disk91/WioLoRaWANFieldTester/helium_logo.h

/*  GIMP header image file format (RGB): /Users/paul/Desktop/helium-hnt-logo.h  */

static unsigned int helium_width = 100;
static unsigned int helium_height = 100;

/*  Call this macro repeatedly.  After each use, the pixel data can be extracted  */

#define HELIUM_PIXEL(data,pixel) {\
pixel[0] = (((data[0] - 33) << 2) | ((data[1] - 33) >> 4)); \
pixel[1] = ((((data[1] - 33) & 0xF) << 4) | ((data[2] - 33) >> 2)); \
pixel[2] = ((((data[2] - 33) & 0x3) << 6) | ((data[3] - 33))); \
data += 4; \
}
static const char *helium_data =
  "````````````````````````````````````````````````````````````````"
  "````````````````````````````````````````````````````````````````"
  "````````````````````````````````^0D`X_L`SN\\`L]\\`G]4`B,L`>L4`2+8`"
  "/+,`/+,`/+,`/+,`2+8`>L4`B,L`G]4`L]``SN\\`XOL`^0D`````````````````"
  "````````````````````````````````````````````````````````````````"
  "````````````````````````````````````````````````````````````````"
  "````````````````````````````````````````````````````````````````"
  "````````````````````````````````````````````````````````````````"
  "````````````````````````````````\\`4`SN\\`H]<`;;``/+,`/+,`/+,`/+,`"
  "/+,`/+,`/+,`/+,`/+,`/+,`/+,`/+,`/+,`/+,`/+,`/+,`/+,`/+,`/+,`/+,`"
  ";;``H]<`S>X`\\`4`````````````````````````````````````````````````"
  "````````````````````````````````````````````````````````````````"
  "````````````````````````````````````````````````````````````````"
  "````````````````````````````````````````````````````````````````"
  "````````````````````````````````````ZO``O.0`<\\(`/+,`/+,`/+,`/+,`"
  "/+,`/+,`/+,`/+,`/+,`/+,`/+,`/+,`/+,`/+,`/+,`/+,`/+,`/+,`/+,`/+,`"
  "/+,`/+,`/+,`/+,`/+,`/+,`/+,`/+,`<\\(`O.0`ZO``````````````````````"
  "````````````````````````````````````````````````````````````````"
  "````````````````````````````````````````````````````````````````"
  "````````````````````````````````````````````````````````````````"
  "````````````````````````````````````````^PH`R.L`>L4`/+,`/+,`/+,`"
  "/+,`/+,`/+,`/+,`/+,`/+,`/+,`/+,`/+,`/+,`/+,`/+,`/+,`/+,`/+,`/+,`"
  "/+,`/+,`/+,`/+,`/+,`/+,`/+,`/+,`/+,`/+,`/+,`/+,`/+,`/+,`/+,`><4`"
  "R.L`^PH`````````````````````````````````````````````````````````"
  "````````````````````````````````````````````````````````````````"
  "````````````````````````````````````````````````````````````````"
  "````````````````````````````````````````````````\\@0`L-X`3;<`/+,`"
  "/+,`/+,`/+,`/+,`/+,`/+,`/+,`/+,`/+,`/+,`/+,`/+,`/+,`/+,`/+,`/+,`"
  "/+,`/+,`/+,`/+,`/+,`/+,`/+,`/+,`/+,`/+,`/+,`/+,`/+,`/+,`/+,`/+,`"
  "/+,`/+,`/+,`/+,`/+,`3;<`K]T`\\@0`````````````````````````````````"
  "````````````````````````````````````````````````````````````````"
  "````````````````````````````````````````````````````````````````"
  "````````````````````````````````````````````````````````\\@0`J=H`"
  "/+,`/+,`/+,`/+,`/+,`/+,`/+,`/+,`/+,`/+,`/+,`/+,`/+,`/+,`/+,`/+,`"
  "/+,`/+,`/+,`/+,`/+,`/+,`/+,`/+,`/+,`/+,`/+,`/+,`/+,`/+,`/+,`/+,`"
  "/+,`/+,`/+,`/+,`/+,`/+,`/+,`/+,`/+,`/+,`/+,`/+,`J=H`\\@0`````````"
  "````````````````````````````````````````````````````````````````"
  "````````````````````````````````````````````````````````````````"
  "````````````````````````````````````````````````````````````````"
  "^`L`L]\\`0;0`/+,`/+,`/+,`/+,`/+,`/+,`/+,`/+,`/+,`/+,`/+,`/+,`/+,`"
  "/+,`/+,`/+,`/+,`/+,`/+,`/+,`/+,`/+,`/+,`/+,`/+,`/+,`/+,`/+,`/+,`"
  "/+,`/+,`/+,`/+,`/+,`/+,`/+,`/+,`/+,`/+,`/+,`/+,`/+,`/+,`/+,`/+,`"
  "/+,`0;0`L]\\`^`L`````````````````````````````````````````````````"
  "````````````````````````````````````````````````````````````````"
  "````````````````````````````````````````````````````````````````"
  "````````````T>``6[H`/+,`/+,`/+,`/+,`/+,`/+,`/+,`/+,`/+,`/+,`/+,`"
  "/+,`/+,`/+,`/+,`/+,`/+,`/+,`/+,`/+,`/+,`/+,`/+,`/+,`/+,`/+,`/+,`"
  "/+,`/+,`/+,`/+,`/+,`/+,`/+,`/+,`/+,`/+,`/+,`/+,`/+,`/+,`/+,`/+,`"
  "/+,`/+,`/+,`/+,`/+,`/+,`/+,`6[H`T>``````````````````````````````"
  "````````````````````````````````````````````````````````````````"
  "````````````````````````````````````````````````````````````````"
  "````````````````````]08`D\\\\`/+,`/+,`/+,`/+,`/+,`/+,`/+,`/+,`/+,`"
  "/+,`/+,`/+,`/+,`/+,`/+,`/+,`/+,`/+,`/+,`/+,`/+,`/+,`/+,`/+,`/+,`"
  "/+,`/+,`/+,`/+,`/+,`/+,`/+,`/+,`/+,`/+,`/+,`/+,`/+,`/+,`/+,`/+,`"
  "/+,`/+,`/+,`/+,`/+,`/+,`/+,`/+,`/+,`/+,`/+,`/+,`/+,`D\\\\`]08`````"
  "````````````````````````````````````````````````````````````````"
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
  "````````````Z?\\`<,$`/+,`/+,`/+,`/+,`/+,`/+,`/+,`5+@`V/4`````````"
  "````````G-0`/+,`/+,`/+,`/+,`/+,`/+,`/+,`/+,`/+,`/+,`/+,`/+,`/+,`"
  "/+,`L]\\`````````````````````````````````````````````\\@0`0;0`/+,`"
  "/+,`/+,`/+,`/+,`/+,`/+,`/+,`/+,`/+,`/+,`/+,`/+,`/+,`/+,`/+,`/+,`"
  "/+,`/+,`/+,`/+,`/+,`/+,`/+,`/+,`/+,`/+,`/+,`/+,`/+,`/+,`/+,`/+,`"
  "/+,`/+,`/+,`/+,`/+,`/+,`/+,`/+,`/+,`/+,`/+,`/+,`/+,`/+,`/+,`/+,`"
  "/+,`/+,`T.``````````````\\00`4[@`/+,`/+,`/+,`/+,`/+,`/+,`/+,`/+,`"
  "/+,`/+,`W/<`````````````[P,`/+,`/+,`/+,`/+,`/+,`/+,`/+,`/+,`/+,`"
  "/+,`/+,`/+,`/+,`/+,`0;0`\\@0`````````````````````````````````````"
  "````J=H`/+,`/+,`/+,`/+,`/+,`/+,`/+,`/+,`/+,`/+,`/+,`/+,`/+,`/+,`"
  "/+,`/+,`/+,`/+,`/+,`/+,`/+,`/+,`/+,`/+,`/+,`/+,`/+,`/+,`/+,`/+,`"
  "/+,`/+,`/+,`/+,`/+,`/+,`/+,`/+,`/+,`/+,`1K4`A,D`A\\H`DL\\`C<T`B,L`"
  "<,$`/+,`/+,`/+,`/+,`6+D`_PT`````````````@<@`/+,`/+,`/+,`/+,`/+,`"
  "/+,`/+,`/+,`/+,`/+,`/+,`6+D`^PH`````````````E,``/+,`/+,`/+,`/+,`"
  "/+,`/+,`/+,`/+,`/+,`/+,`/+,`/+,`/+,`/+,`J=H`````````````````````"
  "````````````````\\@0`/+,`/+,`/+,`/+,`/+,`/+,`/+,`/+,`/+,`/+,`/+,`"
  "/+,`/+,`/+,`/+,`/+,`/+,`/+,`/+,`/+,`/+,`/+,`/+,`/+,`/+,`/+,`/+,`"
  "/+,`/+,`/+,`/+,`/+,`/+,`/+,`/+,`/+,`/+,`7[L`J=H`V/4`\\`8`````````"
  "`````````````````````0X`Y_X`QNH`DL\\`H]<`````````````W/<`/+,`/+,`"
  "/+,`/+,`/+,`/+,`/+,`/+,`/+,`/+,`/+,`/+,`/+,`P.<`````````````RNP`"
  "/+,`/+,`/+,`/+,`/+,`/+,`/+,`/+,`/+,`/+,`/+,`/+,`/+,`/+,`/+,`\\@0`"
  "````````````````````````````````K]T`/+,`/+,`/+,`/+,`/+,`/+,`/+,`"
  "/+,`/+,`/+,`/+,`/+,`/+,`/+,`/+,`/+,`/+,`/+,`/+,`/+,`/+,`/+,`/+,`"
  "/+,`/+,`/+,`/+,`/+,`/+,`/+,`/+,`/+,`/+,`/+,`/+,`D<X`W/<``@\\`````"
  "`````````````````````````````````````````````````````@\\`````````"
  "````I=@`/+,`/+,`/+,`/+,`/+,`/+,`/+,`/+,`/+,`/+,`/+,`/+,`/+,`?<8`"
  "````````````Z?\\`/+,`/+,`/+,`/+,`/+,`/+,`/+,`/+,`/+,`/+,`/+,`/+,`"
  "/+,`/+,`/+,`L-X`````````````````````````````^PH`3;<`/+,`/+,`/+,`"
  "/+,`/+,`/+,`/+,`/+,`/+,`/+,`/+,`/+,`/+,`/+,`/+,`/+,`/+,`/+,`/+,`"
  "/+,`/+,`/+,`/+,`/+,`/+,`/+,`/+,`/+,`/+,`/+,`/+,`/+,`/+,`ALH`Y_X`"
  "````````````````````````````````````````````````````````````````"
  "````````````````````A<D`/+,`/+,`/+,`/+,`/+,`/+,`/+,`/+,`/+,`/+,`"
  "/+,`/+,`/+,`/+,`````````````]P@`/+,`/+,`/+,`/+,`/+,`/+,`/+,`/+,`"
  "/+,`/+,`/+,`/+,`/+,`/+,`/+,`3;<`^PH`````````````````````````R.L`"
  "/+,`/+,`/+,`/+,`/+,`/+,`/+,`/+,`/+,`/+,`/+,`/+,`/+,`/+,`/+,`/+,`"
  "/+,`/+,`/+,`/+,`/+,`/+,`/+,`/+,`/+,`/+,`/+,`/+,`/+,`/+,`/+,`/+,`"
  "4;<`RNP`````````````````````````````````````````````````````````"
  "````````````````````````````````````=<,`/+,`/+,`/+,`/+,`/+,`/+,`"
  "/+,`/+,`/+,`/+,`/+,`/+,`/+,`/+,`````````````_`T`/+,`/+,`/+,`/+,`"
  "/+,`/+,`/+,`/+,`/+,`/+,`/+,`/+,`/+,`/+,`/+,`/+,`R.L`````````````"
  "````````````><4`/+,`/+,`/+,`/+,`/+,`/+,`/+,`/+,`/+,`/+,`/+,`/+,`"
  "/+,`/+,`/+,`/+,`/+,`/+,`/+,`/+,`/+,`/+,`/+,`/+,`/+,`/+,`/+,`/+,`"
  "/+,`/+,`/+,`<L(`[P,`````````````````````````````````````````````"
  "````````````````````````````````````````````````````B,L`/+,`/+,`"
  "/+,`/+,`/+,`/+,`/+,`/+,`/+,`/+,`/+,`/+,`/+,`3[<`````````````\\P4`"
  "/+,`/+,`/+,`/+,`/+,`/+,`/+,`/+,`/+,`/+,`/+,`/+,`/+,`/+,`/+,`/+,`"
  ">L4`````````````````````ZO``/+,`/+,`/+,`/+,`/+,`/+,`/+,`/+,`/+,`"
  "/+,`/+,`/+,`/+,`/+,`/+,`/+,`/+,`/+,`/+,`/+,`/+,`/+,`/+,`/+,`/+,`"
  "/+,`/+,`/+,`/+,`/+,`/+,`CLT`^@H`````````````````````````````````"
  "````````````````````````````````````````````````````````````````"
  "````A\\H`/+,`/+,`/+,`/+,`/+,`/+,`/+,`/+,`/+,`/+,`/+,`/+,`/+,`F],`"
  "````````````Y/P`/+,`/+,`/+,`/+,`/+,`/+,`/+,`/+,`/+,`/+,`/+,`/+,`"
  "/+,`/+,`/+,`/+,`/+,`ZO``````````````````O.0`/+,`/+,`/+,`/+,`/+,`"
  "/+,`/+,`/+,`/+,`/+,`/+,`/+,`/+,`/+,`/+,`/+,`/+,`/+,`/+,`/+,`/+,`"
  "/+,`/+,`/+,`/+,`/+,`/+,`/+,`/+,`/+,`CLT`_PT`````````````````````"
  "````````````````````````````````````````````````````````````````"
  "````````````````_PT`5KD`/+,`/+,`/+,`/+,`/+,`/+,`/+,`/+,`/+,`/+,`"
  "/+,`/+,`/+,`V?4`````````````P^@`/+,`/+,`/+,`/+,`/+,`/+,`/+,`/+,`"
  "/+,`/+,`/+,`/+,`/+,`/+,`/+,`/+,`/+,`O.0`````````````````<\\(`/+,`"
  "/+,`/+,`/+,`/+,`/+,`/+,`/+,`/+,`/+,`/+,`/+,`/+,`/+,`/+,`/+,`/+,`"
  "/+,`/+,`/+,`/+,`/+,`/+,`/+,`/+,`/+,`/+,`/+,`/+,`<L(`^@D`````````"
  "`````````````````````````````````````P\\`Z/\\`S^\\`M-``L]\\`LM\\`O^8`"
  "U_0`]@<`````````````````````````MN$`/+,`/+,`/+,`/+,`/+,`/+,`/+,`"
  "/+,`/+,`/+,`/+,`/+,`/+,`D\\\\`````````````````?L8`/+,`/+,`/+,`/+,`"
  "/+,`/+,`/+,`/+,`/+,`/+,`/+,`/+,`/+,`/+,`/+,`/+,`/+,`<\\(`````````"
  "````\\`4`/+,`/+,`/+,`/+,`/+,`/+,`/+,`/+,`/+,`/+,`/+,`/+,`/+,`/+,`"
  "/+,`/+,`/+,`/+,`/+,`/+,`/+,`/+,`/+,`/+,`/+,`/+,`/+,`/+,`/+,`4;<`"
  "[@(`````````````````````````````````````````\\00`L=\\`7;L`/+,`/+,`"
  "/+,`/+,`/+,`/+,`/+,`/+,`@L@`S^\\`_@P`````\\`4`J=H`/+,`/+,`/+,`/+,`"
  "/+,`/+,`/+,`/+,`/+,`/+,`/+,`/+,`/+,`<\\(`]`@`````````````X?H`/+,`"
  "/+,`/+,`/+,`/+,`/+,`/+,`/+,`/+,`/+,`/+,`/+,`/+,`/+,`/+,`/+,`/+,`"
  "/+,`/+,`\\`4`````````S>X`/+,`/+,`/+,`/+,`/+,`/+,`/+,`/+,`/+,`/+,`"
  "/+,`/+,`/+,`/+,`/+,`/+,`/+,`/+,`/+,`/+,`/+,`/+,`/+,`/+,`/+,`/+,`"
  "/+,`/+,`/+,`R.L`````````````````````````````````````^`L`KMT`/+,`"
  "/+,`/+,`/+,`/+,`/+,`/+,`/+,`/+,`/+,`/+,`/+,`/+,`/+,`/+,`/+,`/+,`"
  "/+,`/+,`/+,`/+,`/+,`/+,`/+,`/+,`/+,`/+,`/+,`/+,`I-@`_0L`````````"
  "`````0X`?\\<`/+,`/+,`/+,`/+,`/+,`/+,`/+,`/+,`/+,`/+,`/+,`/+,`/+,`"
  "/+,`/+,`/+,`/+,`/+,`/+,`SN\\`````````H]<`/+,`/+,`/+,`/+,`/+,`/+,`"
  "/+,`/+,`/+,`/+,`/+,`/+,`/+,`/+,`/+,`/+,`/+,`/+,`/+,`/+,`/+,`/+,`"
  "/+,`/+,`/+,`/+,`/+,`/+,`@L@``P\\`````````````````````````````````"
  "Z/X`;;``/+,`/+,`/+,`/+,`/+,`/+,`/+,`/+,`/+,`/+,`/+,`/+,`/+,`/+,`"
  "/+,`/+,`/+,`/+,`/+,`/+,`/+,`/+,`/+,`<L(`IMD`FM,`ALH`F-(`O^8`[@(`"
  "````````````````````L]``/+,`/+,`/+,`/+,`/+,`/+,`/+,`/+,`/+,`/+,`"
  "/+,`/+,`/+,`/+,`/+,`/+,`/+,`/+,`/+,`/+,`H]<`````````;;``/+,`/+,`"
  "/+,`/+,`/+,`/+,`/+,`/+,`/+,`/+,`/+,`/+,`/+,`/+,`/+,`/+,`/+,`/+,`"
  "/+,`/+,`/+,`/+,`/+,`/+,`/+,`/+,`/+,`/+,`XOL`````````````````````"
  "````````````X_P`4;<`/+,`/+,`/+,`/+,`/+,`/+,`/+,`/+,`/+,`/+,`/+,`"
  "/+,`/+,`/+,`/+,`/+,`/+,`/+,`/+,`/+,`/+,`/+,`4;<`U_0`````````````"
  "````````````````````````````````P.<`/+,`/+,`/+,`/+,`/+,`/+,`/+,`"
  "/+,`/+,`/+,`/+,`/+,`/+,`/+,`/+,`/+,`/+,`/+,`/+,`/+,`/+,`;;``````"
  "^0D`/+,`/+,`/+,`/+,`/+,`/+,`/+,`/+,`/+,`/+,`/+,`/+,`/+,`/+,`/+,`"
  "/+,`/+,`/+,`/+,`/+,`/+,`/+,`/+,`/+,`/+,`/+,`/+,`/+,`BLP`````````"
  "````````````````````````Z/X`4[@`/+,`/+,`/+,`/+,`/+,`/+,`/+,`/+,`"
  "/+,`/+,`/+,`/+,`/+,`/+,`/+,`/+,`/+,`/+,`/+,`/+,`/+,`/+,`/+,`SN\\`"
  "````````````````````````````````````````_@P`IM@`/+,`/+,`/+,`/+,`"
  "/+,`/+,`/+,`/+,`/+,`/+,`/+,`/+,`/+,`/+,`/+,`/+,`/+,`/+,`/+,`/+,`"
  "/+,`/+,`/+,`^0D`X_L`/+,`/+,`/+,`/+,`/+,`/+,`/+,`/+,`/+,`/+,`/+,`"
  "/+,`/+,`/+,`/+,`/+,`/+,`/+,`/+,`/+,`/+,`/+,`/+,`/+,`/+,`/+,`/+,`"
  "/+,`UO0`````````````````````````````^`L`;;``/+,`/+,`/+,`/+,`/+,`"
  "/+,`/+,`/+,`/+,`<,$`B,L`B,L`>,0`/+,`/+,`/+,`/+,`/+,`/+,`/+,`/+,`"
  "/+,`/+,`6KH``@\\`````````````````````````````````_PT`T.``8[T`/+,`"
  "/+,`/+,`/+,`/+,`/+,`/+,`/+,`/+,`/+,`/+,`/+,`/+,`/+,`/+,`/+,`/+,`"
  "/+,`/+,`/+,`/+,`/+,`/+,`/+,`X_L`SN\\`/+,`/+,`/+,`/+,`/+,`/+,`/+,`"
  "/+,`/+,`/+,`/+,`/+,`/+,`/+,`/+,`/+,`/+,`/+,`/+,`/+,`/+,`/+,`/+,`"
  "/+,`/+,`/+,`/+,`5KD`_`T`````````````````````````````K]T`/+,`/+,`"
  "/+,`/+,`/+,`/+,`/+,`4[@`NN,`\\`8`````````````````^0D`QNH`7;L`/+,`"
  "/+,`/+,`/+,`/+,`/+,`/+,`BLP``````````````````````````````P\\`J=H`"
  "6[H`/+,`/+,`/+,`/+,`/+,`/+,`/+,`/+,`/+,`/+,`/+,`/+,`/+,`/+,`/+,`"
  "/+,`/+,`/+,`/+,`/+,`/+,`/+,`/+,`/+,`/+,`/+,`SN\\`L]``/+,`/+,`/+,`"
  "/+,`/+,`/+,`/+,`/+,`/+,`/+,`/+,`/+,`/+,`/+,`/+,`/+,`/+,`/+,`/+,`"
  "/+,`/+,`/+,`/+,`/+,`/+,`/+,`/+,`HM<`````````````````````````````"
  "\\@0`/+,`/+,`/+,`/+,`/+,`/+,`/+,`A<D`]08`````````````````````````"
  "````````^@D`D\\\\`/+,`/+,`/+,`/+,`/+,`/+,`6KH``P\\`````````````````"
  "````````````B\\P`/+,`/+,`/+,`/+,`/+,`/+,`/+,`/+,`/+,`/+,`/+,`/+,`"
  "/+,`/+,`/+,`/+,`/+,`/+,`/+,`/+,`/+,`/+,`/+,`/+,`/+,`/+,`/+,`L]``"
  "G]4`/+,`/+,`/+,`/+,`/+,`/+,`/+,`/+,`/+,`/+,`/+,`/+,`/+,`/+,`/+,`"
  "/+,`/+,`/+,`/+,`/+,`/+,`/+,`/+,`/+,`/+,`/+,`/+,`T.``````````````"
  "````````````````MN$`/+,`/+,`/+,`/+,`/+,`/+,`A,D`_PT`````````````"
  "````````````````````````````_`T`D\\\\`/+,`/+,`/+,`/+,`/+,`/+,`V_8`"
  "````````````````````````````P^@`/+,`/+,`/+,`/+,`/+,`/+,`/+,`/+,`"
  "/+,`/+,`/+,`/+,`/+,`/+,`/+,`/+,`/+,`/+,`/+,`/+,`/+,`/+,`/+,`/+,`"
  "/+,`/+,`/+,`G]4`B,L`/+,`/+,`/+,`/+,`/+,`/+,`/+,`/+,`/+,`/+,`/+,`"
  "/+,`/+,`/+,`/+,`/+,`/+,`/+,`/+,`/+,`/+,`/+,`/+,`/+,`/+,`/+,`/+,`"
  "[@$`````````````````````````````8[T`/+,`/+,`/+,`/+,`/+,`4;<`\\`8`"
  "````````````````````````````````````````````````^@D`7;L`/+,`/+,`"
  "/+,`/+,`/+,`GM4`````````````````````````````Y/P`/+,`/+,`/+,`/+,`"
  "/+,`/+,`/+,`/+,`/+,`/+,`/+,`/+,`/+,`/+,`/+,`/+,`/+,`/+,`/+,`/+,`"
  "/+,`/+,`/+,`/+,`/+,`/+,`/+,`B,L`>L4`/+,`/+,`/+,`/+,`/+,`/+,`/+,`"
  "/+,`/+,`/+,`/+,`/+,`/+,`/+,`/+,`/+,`/+,`/+,`/+,`/+,`/+,`/+,`/+,`"
  "/+,`/+,`/+,`/+,``P\\`````````````````````````[@$`/+,`/+,`/+,`/+,`"
  "/+,`/+,`N.(`````````````````````````````````````````````````````"
  "````R>L`/+,`/+,`/+,`/+,`/+,`1K4``0X`````````````````````````_@P`"
  "/+,`/+,`/+,`/+,`/+,`/+,`/+,`/+,`/+,`/+,`/+,`/+,`/+,`/+,`/+,`/+,`"
  "/+,`/+,`/+,`/+,`/+,`/+,`/+,`/+,`/+,`/+,`/+,`>L4`2+8`/+,`/+,`/+,`"
  "/+,`/+,`/+,`/+,`/+,`/+,`/+,`/+,`/+,`/+,`/+,`/+,`/+,`/+,`/+,`/+,`"
  "/+,`/+,`/+,`/+,`/+,`/+,`/+,`:+X`````````````````````````````T_(`"
  "/+,`/+,`/+,`/+,`/+,`/+,`\\00`````````````````````````````````````"
  "````````````````````^@H`/+,`/+,`/+,`/+,`/+,`/+,`Z?\\`````````````"
  "````````````````7;L`/+,`/+,`/+,`/+,`/+,`/+,`/+,`/+,`/+,`/+,`/+,`"
  "/+,`/+,`/+,`/+,`/+,`/+,`/+,`/+,`/+,`/+,`/+,`/+,`/+,`/+,`/+,`2+8`"
  "/+,`/+,`/+,`/+,`/+,`/+,`/+,`/+,`/+,`/+,`/+,`/+,`/+,`/+,`/+,`/+,`"
  "/+,`/+,`/+,`/+,`/+,`/+,`/+,`/+,`/+,`/+,`/+,`BLP`````````````````"
  "````````````O^8`/+,`/+,`/+,`/+,`/+,`8+P`````````````````````````"
  "````````````````````````````````````````@<@`/+,`/+,`/+,`/+,`/+,`"
  "TO$`````````````````````````````B<L`/+,`/+,`/+,`/+,`/+,`/+,`/+,`"
  "/+,`/+,`/+,`/+,`/+,`/+,`/+,`/+,`/+,`/+,`/+,`/+,`/+,`/+,`/+,`/+,`"
  "/+,`/+,`/+,`/+,`/+,`/+,`/+,`/+,`/+,`/+,`/+,`/+,`/+,`/+,`/+,`/+,`"
  "/+,`/+,`/+,`/+,`/+,`/+,`/+,`/+,`/+,`/+,`/+,`/+,`/+,`/+,`/+,`B,L`"
  "````````````````````````````L-X`/+,`/+,`/+,`/+,`/+,`B,L`````````"
  "````````````````````````````````````````````````````````G-0`/+,`"
  "/+,`/+,`/+,`/+,`TO$`````````````````````````````ALH`/+,`/+,`/+,`"
  "/+,`/+,`/+,`/+,`/+,`/+,`/+,`/+,`/+,`/+,`/+,`/+,`/+,`/+,`/+,`/+,`"
  "/+,`/+,`/+,`/+,`/+,`/+,`/+,`/+,`/+,`/+,`/+,`/+,`/+,`/+,`/+,`/+,`"
  "/+,`/+,`/+,`/+,`/+,`/+,`/+,`/+,`/+,`/+,`/+,`/+,`/+,`/+,`/+,`/+,`"
  "/+,`/+,`/+,`B<L`````````````````````````````M=``/+,`/+,`/+,`/+,`"
  "/+,`B<L`````````````````````````````````````````````````````````"
  "````````G=0`/+,`/+,`/+,`/+,`/+,`TO$`````````````````````````````"
  "ALH`/+,`/+,`/+,`/+,`/+,`/+,`/+,`/+,`/+,`/+,`/+,`/+,`/+,`/+,`/+,`"
  "/+,`/+,`/+,`/+,`/+,`/+,`/+,`/+,`/+,`/+,`/+,`/+,`/+,`/+,`/+,`/+,`"
  "/+,`/+,`/+,`/+,`/+,`/+,`/+,`/+,`/+,`/+,`/+,`/+,`/+,`/+,`/+,`/+,`"
  "/+,`/+,`/+,`/+,`/+,`/+,`/+,`?\\<`````````````````````````````SN\\`"
  "/+,`/+,`/+,`/+,`/+,`7[L`````````````````````````````````````````"
  "````````````````````````@L@`/+,`/+,`/+,`/+,`/+,`TO$`````````````"
  "````````````````B,L`/+,`/+,`/+,`/+,`/+,`/+,`/+,`/+,`/+,`/+,`/+,`"
  "/+,`/+,`/+,`/+,`/+,`/+,`/+,`/+,`/+,`/+,`/+,`/+,`/+,`/+,`/+,`/+,`"
  "2+8`/+,`/+,`/+,`/+,`/+,`/+,`/+,`/+,`/+,`/+,`/+,`/+,`/+,`/+,`/+,`"
  "/+,`/+,`/+,`/+,`/+,`/+,`/+,`/+,`/+,`/+,`/+,`0;0`````````````````"
  "````````````X?H`/+,`/+,`/+,`/+,`/+,`/+,`[`,`````````````````````"
  "````````````````````````````````````^`L`/+,`/+,`/+,`/+,`/+,`/+,`"
  "Y_X`````````````````````````````=<,`/+,`/+,`/+,`/+,`/+,`/+,`/+,`"
  "/+,`/+,`/+,`/+,`/+,`/+,`/+,`/+,`/+,`/+,`/+,`/+,`/+,`/+,`/+,`/+,`"
  "/+,`/+,`/+,`2+8`>L4`/+,`/+,`/+,`/+,`/+,`/+,`/+,`/+,`/+,`/+,`/+,`"
  "/+,`/+,`/+,`/+,`/+,`/+,`/+,`/+,`/+,`/+,`/+,`/+,`/+,`/+,`/+,`/+,`"
  "]@<`````````````````````````_0L`/+,`/+,`/+,`/+,`/+,`/+,`MN$`````"
  "````````````````````````````````````````````````````R^T`/+,`/+,`"
  "/+,`/+,`/+,`/[0`_@P``````````````````````````P\\`/+,`/+,`/+,`/+,`"
  "/+,`/+,`/+,`/+,`/+,`/+,`/+,`/+,`/+,`/+,`/+,`/+,`/+,`/+,`/+,`/+,`"
  "/+,`/+,`/+,`/+,`/+,`/+,`/+,`>L4`B,L`/+,`/+,`/+,`/+,`/+,`/+,`/+,`"
  "/+,`/+,`/+,`/+,`/+,`/+,`/+,`/+,`/+,`/+,`/+,`/+,`/+,`/+,`/+,`/+,`"
  "/+,`/+,`/+,`/+,`W?@`````````````````````````````EM$`/+,`/+,`/+,`"
  "/+,`/+,`3[<`\\P4`````````````````````````````````````````````````"
  "^PH`8+P`/+,`/+,`/+,`/+,`/+,`E,``````````````````````````````[@(`"
  "/+,`/+,`/+,`/+,`/+,`/+,`/+,`/+,`/+,`/+,`/+,`/+,`/+,`/+,`/+,`/+,`"
  "/+,`/+,`/+,`/+,`/+,`/+,`/+,`/+,`/+,`/+,`/+,`B,L`G]4`/+,`/+,`/+,`"
  "/+,`/+,`/+,`/+,`/+,`/+,`/+,`/+,`/+,`/+,`/+,`/+,`/+,`/+,`/+,`/+,`"
  "/+,`/+,`/+,`/+,`/+,`/+,`/+,`/+,`N>,`````````````````````````````"
  "V/4`/+,`/+,`/+,`/+,`/+,`/+,`@L@`_PT`````````````````````````````"
  "````````````_`T`D\\\\`/+,`/+,`/+,`/+,`/+,`/+,`T_(`````````````````"
  "````````````S^\\`/+,`/+,`/+,`/+,`/+,`/+,`/+,`/+,`/+,`/+,`/+,`/+,`"
  "/+,`/+,`/+,`/+,`/+,`/+,`/+,`/+,`/+,`/+,`/+,`/+,`/+,`/+,`/+,`G]4`"
  "L]``/+,`/+,`/+,`/+,`/+,`/+,`/+,`/+,`/+,`/+,`/+,`/+,`/+,`/+,`/+,`"
  "/+,`/+,`/+,`/+,`/+,`/+,`/+,`/+,`/+,`/+,`/+,`/+,`<L(`````````````"
  "`````````````````@\\`0;0`/+,`/+,`/+,`/+,`/+,`/+,`A<D`]08`````````"
  "````````````````````````^@D`D\\\\`/+,`/+,`/+,`/+,`/+,`/+,`:+X`_`T`"
  "````````````````````````````H-8`/+,`/+,`/+,`/+,`/+,`/+,`/+,`/+,`"
  "/+,`/+,`/+,`/+,`/+,`/+,`/+,`/+,`/+,`/+,`/+,`/+,`/+,`/+,`/+,`/+,`"
  "/+,`/+,`/+,`L]``SN\\`/+,`/+,`/+,`/+,`/+,`/+,`/+,`/+,`/+,`/+,`/+,`"
  "/+,`/+,`/+,`/+,`/+,`/+,`/+,`/+,`/+,`/+,`/+,`/+,`/+,`/+,`/+,`5KD`"
  "HM<`^@H`````````````````````````````7;L`/+,`/+,`/+,`/+,`/+,`/+,`"
  "/+,`4[@`NN,`\\`8`````````````````^0D`QNH`7;L`/+,`/+,`/+,`/+,`/+,`"
  "/+,`/+,`U/(`````````````````````````````_@P`4;<`/+,`/+,`/+,`/+,`"
  "/+,`/+,`/+,`/+,`/+,`/+,`/+,`/+,`/+,`/+,`/+,`/+,`/+,`/+,`/+,`/+,`"
  "/+,`/+,`/+,`/+,`/+,`/+,`/+,`SN\\`X_L`/+,`/+,`/+,`/+,`/+,`/+,`/+,`"
  "/+,`/+,`/+,`/+,`/+,`/+,`/+,`/+,`/+,`/+,`/+,`/+,`/+,`/+,`/+,`/+,`"
  "/+,`9;T`S^\\`_PT`````````````````````````````````^@D`/+,`/+,`/+,`"
  "/+,`/+,`/+,`/+,`/+,`/+,`/+,`/+,`<,$`B,L`B,L`>,0`/+,`/+,`/+,`/+,`"
  "/+,`/+,`/+,`/+,`/+,`F],`````````````````````````````````T_(`/+,`"
  "/+,`/+,`/+,`/+,`/+,`/+,`/+,`/+,`/+,`/+,`/+,`/+,`/+,`/+,`/+,`/+,`"
  "/+,`/+,`/+,`/+,`/+,`/+,`/+,`/+,`/+,`/+,`/+,`X_L`^0D`/+,`/+,`/+,`"
  "/+,`/+,`/+,`/+,`/+,`/+,`/+,`/+,`/+,`/+,`/+,`/+,`/+,`/+,`/+,`/+,`"
  "/+,`/+,`/+,`/+,`I-@`_@P`````````````````````````````````````````"
  "M=``/+,`/+,`/+,`/+,`/+,`/+,`/+,`/+,`/+,`/+,`/+,`/+,`/+,`/+,`/+,`"
  "/+,`/+,`/+,`/+,`/+,`/+,`/+,`/+,`=L,`_0L`````````````````````````"
  "````````@\\D`/+,`/+,`/+,`/+,`/+,`/+,`/+,`/+,`/+,`/+,`/+,`/+,`/+,`"
  "/+,`/+,`/+,`/+,`/+,`/+,`/+,`/+,`/+,`/+,`/+,`/+,`/+,`/+,`/+,`^0D`"
  "````;;``/+,`/+,`/+,`/+,`/+,`/+,`/+,`/+,`/+,`/+,`/+,`/+,`/+,`/+,`"
  "/+,`/+,`/+,`/+,`/+,`/+,`/+,`L]``````````````````````````````````"
  "````````_@P`NN,`/+,`/+,`/+,`/+,`/+,`/+,`/+,`/+,`/+,`/+,`/+,`/+,`"
  "/+,`/+,`/+,`/+,`/+,`/+,`/+,`/+,`/+,`/+,`/+,`>,0`]@<`````````````"
  "````````````````````V_8`/+,`/+,`/+,`/+,`/+,`/+,`/+,`/+,`/+,`/+,`"
  "/+,`/+,`/+,`/+,`/+,`/+,`/+,`/+,`/+,`/+,`/+,`/+,`/+,`/+,`/+,`/+,`"
  "/+,`/+,`;;``````````H]<`/+,`/+,`/+,`/+,`/+,`/+,`/+,`/+,`/+,`/+,`"
  "/+,`/+,`/+,`/+,`/+,`/+,`/+,`/+,`/+,`/+,`K-P`````````````````_`T`"
  "T.``E]$`5KD`/+,`;+``B<L`2+8`/+,`/+,`/+,`/+,`/+,`/+,`/+,`/+,`/+,`"
  "/+,`/+,`/+,`/+,`/+,`/+,`/+,`/+,`/+,`/+,`/+,`/+,`/+,`/+,`G]4`_@P`"
  "`````````````````````````````````0X`><4`/+,`/+,`/+,`/+,`/+,`/+,`"
  "/+,`/+,`/+,`/+,`/+,`/+,`/+,`/+,`/+,`/+,`/+,`/+,`/+,`/+,`/+,`/+,`"
  "/+,`/+,`/+,`/+,`/+,`/+,`I-@`````````S>X`/+,`/+,`/+,`/+,`/+,`/+,`"
  "/+,`/+,`/+,`/+,`/+,`/+,`/+,`/+,`/+,`/+,`/+,`/+,`/+,`=L,`_`T`````"
  "````````Z?\\`=<,`/+,`/+,`/+,`/+,`/+,`/+,`/+,`/+,`/+,`/+,`/+,`/+,`"
  "/+,`:K\\`ALH`<<$`/+,`/+,`/+,`/+,`/+,`/+,`/+,`/+,`/+,`/+,`/+,`/+,`"
  "<<$`V/4`````````````````````````````````````````P><`/+,`/+,`/+,`"
  "/+,`/+,`/+,`/+,`/+,`/+,`/+,`/+,`/+,`/+,`/+,`/+,`/+,`/+,`/+,`/+,`"
  "/+,`/+,`/+,`/+,`/+,`/+,`/+,`/+,`/+,`/+,`SN\\`````````\\`4`/+,`/+,`"
  "/+,`/+,`/+,`/+,`/+,`/+,`/+,`/+,`/+,`/+,`/+,`/+,`/+,`/+,`/+,`/+,`"
  "/+,`V?4`````````````Z/X`4[@`/+,`/+,`/+,`/+,`/+,`/+,`/+,`/+,`/+,`"
  "/+,`/+,`/+,`4[@`U_0`````````````Y?P`J=H`7;L`/+,`/+,`/+,`/+,`/+,`"
  "/+,`2+8`GM4`V/4``@\\`````````````````````````````````````````YOT`"
  "/[0`/+,`/+,`/+,`/+,`/+,`/+,`/+,`/+,`/+,`/+,`/+,`/+,`/+,`/+,`/+,`"
  "/+,`/+,`/+,`/+,`/+,`/+,`/+,`/+,`/+,`/+,`/+,`/+,`/+,`/+,`\\`4`````"
  "````````<\\(`/+,`/+,`/+,`/+,`/+,`/+,`/+,`/+,`/+,`/+,`/+,`/+,`/+,`"
  "/+,`/+,`/+,`/+,`;;``````````````_@P`;+``/+,`/+,`/+,`/+,`/+,`/+,`"
  "/+,`/+,`/+,`/+,`/+,`/+,`/+,`V_8`````````````````````````````\\00`"
  "V_8`TO$`TO$`U_0`[0$``P\\`````````````````````````````````````````"
  "````````]P<`9KX`/+,`/+,`/+,`/+,`/+,`/+,`/+,`/+,`/+,`/+,`/+,`/+,`"
  "/+,`/+,`/+,`/+,`/+,`/+,`/+,`/+,`/+,`/+,`/+,`/+,`/+,`/+,`/+,`/+,`"
  "/+,`<\\(`````````````````O.0`/+,`/+,`/+,`/+,`/+,`/+,`/+,`/+,`/+,`"
  "/+,`/+,`/+,`/+,`/+,`/+,`/+,`/+,`O.0`````````````Q^H`/+,`/+,`/+,`"
  "/+,`/+,`/+,`/+,`/+,`/+,`/+,`/+,`/+,`/+,`;L$`````````````````````"
  "````````````````````````````````````````````````````````````````"
  "````````````````````]P@`<L(`/+,`/+,`/+,`/+,`/+,`/+,`/+,`/+,`/+,`"
  "/+,`/+,`/+,`/+,`/+,`/+,`/+,`/+,`/+,`/+,`/+,`/+,`/+,`/+,`/+,`/+,`"
  "/+,`/+,`/+,`/+,`/+,`O.0`````````````````ZO``/+,`/+,`/+,`/+,`/+,`"
  "/+,`/+,`/+,`/+,`/+,`/+,`/+,`/+,`/+,`/+,`/+,`/+,`W?@`````````````"
  "?<8`/+,`/+,`/+,`/+,`/+,`/+,`/+,`/+,`/+,`/+,`/+,`/+,`/+,`FM,`````"
  "````````````````````````````````````````````````````````````````"
  "````````````````````````````````]@<`<L(`/+,`/+,`/+,`/+,`/+,`/+,`"
  "/+,`/+,`/+,`/+,`/+,`/+,`/+,`/+,`/+,`/+,`/+,`/+,`/+,`/+,`/+,`/+,`"
  "/+,`/+,`/+,`/+,`/+,`/+,`/+,`/+,`/+,`ZO``````````````````````><4`"
  "/+,`/+,`/+,`/+,`/+,`/+,`/+,`/+,`/+,`/+,`/+,`/+,`/+,`/+,`/+,`/+,`"
  "[0$``````````@\\`/+,`/+,`/+,`/+,`/+,`/+,`/+,`/+,`/+,`/+,`/+,`/+,`"
  "/+,`/+,`D,X`````````````````````````````````````````````````````"
  "````````````````````````````````````````````Y/P`9;T`/+,`/+,`/+,`"
  "/+,`/+,`/+,`/+,`/+,`/+,`/+,`/+,`/+,`/+,`/+,`/+,`/+,`/+,`/+,`/+,`"
  "/+,`/+,`/+,`/+,`/+,`/+,`/+,`/+,`/+,`/+,`/+,`/+,`>L4`````````````"
  "````````````R.L`/+,`/+,`/+,`/+,`/+,`/+,`/+,`/+,`/+,`/+,`/+,`/+,`"
  "/+,`/+,`/+,`/+,`\\P4`````````]P<`/+,`/+,`/+,`/+,`/+,`/+,`/+,`/+,`"
  "/+,`/+,`/+,`/+,`/+,`/+,`B,L`````````````````````````````````````"
  "````````````````````````````````````````````````````_`T`O>4`/+,`"
  "/+,`/+,`/+,`/+,`/+,`/+,`/+,`/+,`/+,`/+,`/+,`/+,`/+,`/+,`/+,`/+,`"
  "/+,`/+,`/+,`/+,`/+,`/+,`/+,`/+,`/+,`/+,`/+,`/+,`/+,`/+,`/+,`/+,`"
  "R.L`````````````````````````^PH`3;<`/+,`/+,`/+,`/+,`/+,`/+,`/+,`"
  "/+,`/+,`/+,`/+,`/+,`/+,`/+,`/+,`[@$``````````@\\`/+,`/+,`/+,`/+,`"
  "/+,`/+,`/+,`/+,`/+,`/+,`/+,`/+,`/+,`/+,`E,``````````````````````"
  "````````````````````````````````````````````````````````````````"
  "U_0`<\\(`/+,`/+,`/+,`/+,`/+,`/+,`/+,`/+,`/+,`/+,`/+,`/+,`/+,`/+,`"
  "/+,`/+,`/+,`/+,`/+,`/+,`/+,`/+,`/+,`/+,`/+,`/+,`/+,`/+,`/+,`/+,`"
  "/+,`/+,`/+,`3;<`^PH`````````````````````````````L-X`/+,`/+,`/+,`"
  "/+,`/+,`/+,`/+,`/+,`/+,`/+,`/+,`/+,`/+,`/+,`/+,`X_L`````````````"
  ">L4`/+,`/+,`/+,`/+,`/+,`/+,`/+,`/+,`/+,`/+,`/+,`/+,`/+,`P><`````"
  "````````^`L`````````````````````````````````````````````````````"
  "````^`L`S>X`><4`/+,`/+,`/+,`/+,`/+,`/+,`/+,`/+,`/+,`/+,`/+,`/+,`"
  "/+,`/+,`/+,`/+,`/+,`/+,`/+,`/+,`/+,`/+,`/+,`/+,`/+,`/+,`/+,`/+,`"
  "/+,`/+,`/+,`/+,`/+,`/+,`/+,`L-X`````````````````````````````````"
  "\\@0`/+,`/+,`/+,`/+,`/+,`/+,`/+,`/+,`/+,`/+,`/+,`/+,`/+,`/+,`/+,`"
  "Q.D`````````````QNH`/+,`/+,`/+,`/+,`/+,`/+,`/+,`/+,`/+,`/+,`/+,`"
  "/+,`/+,`\\@0`````````````JML`;+``L]``V_8`\\@0`````````````````````"
  "````_@P`Y_X`Q^L`FM,`1+4`/+,`/+,`/+,`/+,`/+,`/+,`/+,`/+,`/+,`/+,`"
  "/+,`/+,`/+,`/+,`/+,`/+,`/+,`/+,`/+,`/+,`/+,`/+,`/+,`/+,`/+,`/+,`"
  "/+,`/+,`/+,`/+,`/+,`/+,`/+,`/+,`/+,`/+,`/+,`\\@0`````````````````"
  "````````````````````J=H`/+,`/+,`/+,`/+,`/+,`/+,`/+,`/+,`/+,`/+,`"
  "/+,`/+,`/+,`/+,`A<D`````````````_@P`;+``/+,`/+,`/+,`/+,`/+,`/+,`"
  "/+,`/+,`/+,`/+,`/+,`K=P``````````````@\\`8KP`/+,`/+,`/+,`/+,`/+,`"
  "<,$`BLP`BLP`@L@`2[8`/+,`/+,`/+,`/+,`/+,`/+,`/+,`/+,`/+,`/+,`/+,`"
  "/+,`/+,`/+,`/+,`/+,`/+,`/+,`/+,`/+,`/+,`/+,`/+,`/+,`/+,`/+,`/+,`"
  "/+,`/+,`/+,`/+,`/+,`/+,`/+,`/+,`/+,`/+,`/+,`/+,`/+,`/+,`J=H`````"
  "````````````````````````````````````\\@0`0;0`/+,`/+,`/+,`/+,`/+,`"
  "/+,`/+,`/+,`/+,`/+,`/+,`/+,`/+,`/+,`ZO``````````````Z/X`4[@`/+,`"
  "/+,`/+,`/+,`/+,`/+,`/+,`/+,`/+,`@L@`_PT`````````````UO,`/+,`/+,`"
  "/+,`/+,`/+,`/+,`/+,`/+,`/+,`/+,`/+,`/+,`/+,`/+,`/+,`/+,`/+,`/+,`"
  "/+,`/+,`/+,`/+,`/+,`/+,`/+,`/+,`/+,`/+,`/+,`/+,`/+,`/+,`/+,`/+,`"
  "/+,`/+,`/+,`/+,`/+,`/+,`/+,`/+,`/+,`/+,`/+,`/+,`/+,`/+,`/+,`/+,`"
  "/+,`0;0`\\@0`````````````````````````````````````````````L]\\`/+,`"
  "/+,`/+,`/+,`/+,`/+,`/+,`/+,`/+,`/+,`/+,`/+,`/+,`/+,`D<X`````````"
  "````````ZO``=\\0`/+,`/+,`/+,`/+,`/+,`/+,`/+,`GM4`_0L`````````````"
  "_`T`=L,`/+,`/+,`/+,`/+,`/+,`/+,`/+,`/+,`/+,`/+,`/+,`/+,`/+,`/+,`"
  "/+,`/+,`/+,`/+,`/+,`/+,`/+,`/+,`/+,`/+,`/+,`/+,`/+,`/+,`/+,`/+,`"
  "/+,`/+,`/+,`/+,`/+,`/+,`/+,`/+,`/+,`/+,`/+,`/+,`/+,`/+,`/+,`/+,`"
  "/+,`/+,`/+,`/+,`/+,`L]\\`````````````````````````````````````````"
  "````````^`L`6[H`/+,`/+,`/+,`/+,`/+,`/+,`/+,`/+,`/+,`/+,`/+,`/+,`"
  "/+,`/+,`RNP``````````````````0X`TO$`FM,`:+X`/+,`>L4`J=H`YOT`````"
  "````````````````L]``/+,`/+,`/+,`/+,`/+,`/+,`/+,`/+,`/+,`/+,`/+,`"
  "/+,`/+,`/+,`/+,`/+,`/+,`/+,`/+,`/+,`/+,`/+,`/+,`/+,`/+,`/+,`/+,`"
  "/+,`/+,`/+,`/+,`/+,`/+,`/+,`/+,`/+,`/+,`/+,`/+,`/+,`/+,`/+,`/+,`"
  "/+,`/+,`/+,`/+,`/+,`/+,`/+,`/+,`6[H`^`L`````````````````````````"
  "````````````````````````````T?$`/+,`/+,`/+,`/+,`/+,`/+,`/+,`/+,`"
  "/+,`/+,`/+,`/+,`/+,`/+,`0;0`W?<`````````````````````````````````"
  "````````````````````````````T.``/+,`/+,`/+,`/+,`/+,`/+,`/+,`/+,`"
  "/+,`/+,`/+,`/+,`/+,`/+,`/+,`/+,`/+,`/+,`/+,`/+,`/+,`/+,`/+,`/+,`"
  "/+,`/+,`/+,`/+,`/+,`/+,`/+,`/+,`/+,`/+,`/+,`/+,`/+,`/+,`/+,`/+,`"
  "/+,`/+,`/+,`/+,`/+,`/+,`/+,`/+,`/+,`/+,`/+,`/+,`T?$`````````````"
  "````````````````````````````````````````````````D\\\\`/+,`/+,`/+,`"
  "/+,`/+,`/+,`/+,`/+,`/+,`/+,`/+,`/+,`/+,`/+,`1+4`S>X`````````````"
  "`````````````````````````````````````@\\`NN,`/+,`/+,`/+,`/+,`/+,`"
  "/+,`/+,`/+,`/+,`/+,`/+,`/+,`/+,`/+,`/+,`/+,`/+,`/+,`/+,`/+,`/+,`"
  "/+,`/+,`/+,`/+,`/+,`/+,`/+,`/+,`/+,`/+,`/+,`/+,`/+,`/+,`/+,`/+,`"
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
  "````````````````^0D`X_L`SN\\`L]``G]4`B,L`>L4`2+8`/+,`/+,`/+,`/+,`"
  "2+8`>L4`B,L`G]4`L]``SN\\`X_L`^0D`````````````````````````````````"
  "````````````````````````````````````````````````````````````````"
  "````````````````````````````````````````````````````````````````"
  "";
