disk91/WioLoRaWANFieldTester/ttn_logo.h

/*  GIMP header image file format (RGB): /Users/paul/Desktop/ttn.h  */

static unsigned int ttn_width = 100;
static unsigned int ttn_height = 85;

/*  Call this macro repeatedly.  After each use, the pixel data can be extracted  */

#define TTN_PIXEL(data,pixel) {\
pixel[0] = (((data[0] - 33) << 2) | ((data[1] - 33) >> 4)); \
pixel[1] = ((((data[1] - 33) & 0xF) << 4) | ((data[2] - 33) >> 2)); \
pixel[2] = ((((data[2] - 33) & 0x3) << 6) | ((data[3] - 33))); \
data += 4; \
}
static const char *ttn_data =
  "````````````````````````````````````````````````````````````````"
  "````````````````````````````````````````````````````````````````"
  "`````````````````````````````````````````````````````````@\\`Y0(`"
  "P/0`G.@`>=X`6]@`2]4`5M<`<]P`E>4`N>``W?\\`_PX`````````````````````"
  "````````````````````````````````````````````````````````````````"
  "````````````````````````````````````````````````````````````````"
  "````````````````````````````````````````````````````````````````"
  "````````````````````````````````````````````````````````````````"
  "````````````````````````````````````````````````````````````````"
  "]`H`O/,`:=P`2]8`2M8`2M8`2M8`2=4`2=4`2=4`2-4`2-4`1]0`1]0`6M<`KNT`"
  "[P8`````````````````````````````````````````````````````````````"
  "X?``L>P`O_$`T_D`ZP0``0\\`````````````````````````````````````````"
  "````````````````````````````````````````````````````````````````"
  "````````````````````````````````````````````````````````````````"
  "````````````````````````````````````````````````````````````````"
  "````````_PX`OO,`6-D`2]<`2]8`2M8`2M8`2M8`2=4`2=4`2=4`2-4`2-4`2-0`"
  "1]0`1]0`1]0`1M,`1M,`J^L`]`H`````````````````````````````````````"
  "````````````\\0<`0\\``0,\\`0,\\`/\\\\`/\\\\`2<``EN$`R?4`]PH`````````````"
  "````````````````````````````````````````````````````````````````"
  "````````````````````````````````````````````````````````````````"
  "````````````````````````````````````````````````````````````````"
  "````````````````````Z`4`?-``2]<`2]<`2]<`2M8`2M8`2M8`2=8`2=4`2=4`"
  "2-4`2-4`2-0`1]0`1]0`1]0`1M0`1M,`1M,`1=,`8=<`V_X`````````````````"
  "````````````````````````````X/\\`0,``0,\\`0,\\`/\\\\`/\\\\`/LX`/LX`/LX`"
  "0,X`F^,`XO``````````````````````````````````````````````````````"
  "````````````````````````````````````````````````````````````````"
  "````````````````````````````````````````````````````````````````"
  "````````````````````````````````V?X`6=D`3-<`2]<`2]<`2]8`2M8`2M8`"
  "2=8`2=4`2=4`2-4`2-4`2-0`1]0`1]0`1]0`1M0`1M,`1M,`1=,`1=,`1=(`1-(`"
  "O_(``````````````````````````````````````````0\\`G.4`0,\\`/\\\\`/\\\\`"
  "/\\X`/LX`/LX`/LX`/<X`/<T`/,T`B]X`Z0,`````````````````````````````"
  "````````````````````````````````````````````````````````````````"
  "````````````````````````````````````````````````````````````````"
  "````````````````````````````````````````````U/P`3-<`3-<`2]<`2]8`"
  "2]8`2M8`2M8`2M8`2=8`2=4`2=4`2-4`2-4`2-0`1]0`1]0`1]0`1M,`1M,`1M,`"
  "1=,`1=,`1=(`1-(`1-(`MN\\`````````````````````````````````````````"
  "`````0X`[`8`WOX`PO(`E.$`0\\\\`/<X`/<X`/<T`/,T`/,T`/,P`KND`_@T`````"
  "````````````````````````````````````````````````````````````````"
  "````````````````````````````````````````````````````````````````"
  "````````````````````````````````````````````````````````X@$`4-@`"
  "3-<`3-<`2]<`2]8`2]8`2M8`2M8`2M8`2=4`2=4`2=4`2-4`2-4`1]0`1]0`1]0`"
  "1M0`1M,`1M,`1M,`1=,`1=(`1-(`1-(`1-(`0](`QO4`````````````````````"
  "````````````````````````````````````````^`P`T/@`@ML`/<T`/,T`/,T`"
  ".\\P`.\\P`<M8`ZP,`````````````````````````````````````````````````"
  "````````````````````````````````````````````````````````````````"
  "````````````````````````````````````````````````````````````````"
  "````]@H`9MP`3-<`3-<`2]<`2]<`2]8`2M8`2M8`2M8`2=8`2=4`2=4`2-4`2-4`"
  "2-0`1]0`1]0`1]0`1M0`1M,`1M,`1=,`1=,`1=(`1-(`1-(`1-(`0](`1=$`Y0$`"
  "`````````````````````````````0X`Z0,`\\08``0\\`````````````````````"
  "````X/\\`@ML`/,T`.\\P`.\\P`.\\P`2<X`U_H`````````````````````````````"
  "````````````````````````````````````````````````````````````````"
  "````````````````````````````````````````````````````````````````"
  "````````````````````F^@`3-<`3-<`3-<`2]<`2]<`2]8`2M8`2M8`2M8`2=4`"
  "2=4`2=4`2-4`2-0`2-0`1]0`1]0`1M0`1M,`1M,`1M,`1=,`1=,`1=(`1-(`1-(`"
  "0](`0](`0]$`<]H`_PX`````````````````````_`X`?ML`/\\\\`/\\\\`/\\\\`@=L`"
  "MNT`X?```P```````````````P\\`S/8`5,``.\\P`.LP`.LP`.LL`S?8`````````"
  "````````````````````````````````````````````````````````````````"
  "````````````````````````````````````````````````````````````````"
  "````````````````````````````````W?``3=@`3-<`3-<`3-<`2]<`2]<`2]8`"
  "2M8`2M8`2=8`2=4`2=4`2-4`2-4`2-0`1]0`1]0`1]0`1M0`1M,`1M,`1=,`1=,`"
  "1=(`1-(`1-(`1-(`0](`0]$`0]$`0M$`P/(`````````````````````Y@(`0,\\`"
  "/\\\\`/\\\\`/\\\\`/LX`/LX`/LX`:=4`Q/(`_0P`````````````\\@<`?=D`.LP`.LP`"
  ".LL`.<L`T?<`````````````````````````````````````````````````````"
  "````````````````````````````````````````````````````````````````"
  "````]0H`Y@,`W?``WO``Z00`]`L`````````````````````AN,`3-<`3-<`3-<`"
  "2]<`2]<`2]8`2M8`2M8`2M8`2=4`2=4`2=4`2-4`2-4`1]0`1]0`1]0`1M0`1M,`"
  "1M,`1=,`1=,`1=(`1-(`1-(`1-(`0](`0]$`0]$`0M$`0M$`7-4`_0T`````````"
  "````````_0P`9M4`/\\\\`/\\\\`/LX`/LX`/LX`/<X`/<T`/<T`7](`S?8``P``````"
  "````_@T`F.$`.LL`.<L`.<L`/,L`W_X`````````````````````````````````"
  "````````````````````````````````````````````````````````````````"
  "````_PX`UOX`HNP`9-T`4-H`4-H`4-H`3]D`3]D`3MD`;=X`J^X`W?```@\\`YP,`"
  "3=@`3-<`3-<`2]<`2]<`2]8`2M8`2M8`2M8`2=4`2=4`2=4`2-4`2-4`2-0`1]0`"
  "1]0`1]0`1M,`1M,`1M,`1=,`1=,`1=(`1-(`1-(`1-(`0]$`0]$`0M$`0M$`0M$`"
  "0<``R_8`````````````````````^0H`U/H`P/$`H>4`8]0`/<X`/<T`/<T`/,T`"
  "/,T`/,T`CMX`]@D``````````0\\`G>(`.<L`.<L`.<L`5LX`\\`@`````````````"
  "````````````````````````````````````````````````````````````````"
  "````````````_PX`Q?<`:=\\`4=L`4=H`4-H`4-H`4-H`3]D`3]D`3]D`3MD`3MD`"
  "3M@`3=@`=-\\`CN4`3-<`3-<`3-<`2]<`2]8`2]8`2M8`2M8`2M8`2=4`2=4`2=4`"
  "2-4`2-4`1]0`1]0`1]0`1M0`1M,`1M,`1=,`1=,`1=(`1-(`1-(`1-(`0](`0]$`"
  "0]$`0M$`0M$`0M$`0<``B]\\`````````````````````````````````````````"
  "Y`(`K^H`2\\\\`/,T`/,T`.\\P`.\\P`8],`YP(``````````0X`C]X`.<L`.,H`.,H`"
  "B=L``@\\`````````````````````````````````````````````````````````"
  "````````````````````````Y0,`>>(`4ML`4=L`4=H`4=H`4-H`4-H`3]D`3]D`"
  "3]D`3MD`3M@`3M@`3=@`3=@`3=@`3-<`3-<`3-<`2]<`2]<`2]8`2M8`2M8`2M8`"
  "2=8`2=4`2=4`2-4`2-4`2-0`1]0`1]0`1]0`1M,`1M,`1M,`1=,`1=,`1-(`1-(`"
  "1-(`1-(`0]$`0]$`0]$`0M$`0M$`0<``0<``0<``^0L`````````````````````"
  "````````````````````````]`H`K.D`/,T`.\\P`.\\P`.\\P`3<\\`X?\\`````````"
  "^@L`:M0`.,H`.,H`-\\H`RO0`````````````````````````````````````````"
  "````````````````````````````````````R?D`5-L`4ML`4=L`4=L`4=H`4-H`"
  "4-H`4-H`3]D`3]D`3]D`3MD`3MD`3M@`3=@`3=@`3=@`3-<`3-<`3-<`2]<`2]<`"
  "2]8`2M8`2M8`2M8`2=4`2=4`2=4`2-4`2-0`2-0`1]0`1]0`1M0`1M,`1M,`1=,`"
  "1=,`1=,`1-(`1-(`1-(`0](`0]$`0]$`0M$`0M$`0M$`0<``0<``0<``W?X`````"
  "`````0X`[@4`X/\\`W_\\`Z@,`_0T`````````````````````XO``9M,`.\\P`.\\P`"
  ".LP`3<X`Z@,`````````Y@$`.,H`.,H`-\\H`5<X`^PL`````````````````````"
  "````````````````````````````````````````````````O?4`4ML`4ML`4ML`"
  "4=L`4=H`4=H`4-H`4-H`4-H`3]D`3]D`3]D`3MD`3M@`3=@`3=@`3=@`3=@`3-<`"
  "3-<`2]<`2]<`2]8`2M8`2M8`2M8`2=8`2=4`2=4`2-4`2-4`2-0`1]0`1]0`1]0`"
  "1M0`1M,`1M,`1=,`1=,`1=(`1-(`1-(`1-(`0](`0]$`0]$`0M$`0M$`0L``0<``"
  "0<``0<``P_,`UOL`EN(`2<``/\\\\`/LX`/LX`/LX`/<X`AMT`R/0`^`P`````````"
  "````]PH`?=D`.LP`.LP`.LL`9=(`]`H`````````K^@`.,H`-\\H`-\\H`N.P`````"
  "````````````````````````````````````````````````````````````SOL`"
  "4ML`4ML`4ML`4=L`4=L`4=H`4=H`4-H`4-H`4-H`3]D`3]D`3MD`3MD`3M@`3=@`"
  "3=@`3=@`3-<`3-<`3-<`2]<`2]<`2]8`2M8`2M8`2M8`2=4`2=4`2=4`2-4`2-4`"
  "2-0`1]0`1]0`1M0`1M,`1M,`1=,`1=,`1=,`1-(`1-(`1-(`0](`0]$`0]$`0]$`"
  "0M$`0M$`0<``0<``0<``0,``0,``0,\\`/\\\\`/\\\\`/\\\\`/LX`/LX`/LX`/<X`/<T`"
  "/,T`6M$`S/8`````````````^@L`>=@`.LL`.LL`.<L`E]``````````^PL`4\\X`"
  "-\\H`-\\D`4<T`_0P`````````````````````````````````````````````````"
  "````````ZP8`6-T`4ML`4ML`4ML`4=L`4=H`4=H`4-H`4-H`4-H`3]D`3]D`3]D`"
  "3MD`3MD`3M@`3=@`3=@`3=@`3-<`3-<`2]<`2]<`2]8`2]8`2M8`2M8`2=8`2=4`"
  "2=4`2-4`2-4`2-4`1]0`1]0`1]0`1M0`1M,`1M,`1=,`1=,`1=(`1-(`1-(`1-(`"
  "0](`0]$`0]$`0M$`0M$`0L``0<``0<``0<``0,``0,\\`0,\\`/\\\\`/\\\\`/LX`/LX`"
  "/LX`/<X`/<X`/<T`/<T`/,T`/,T`F^(`_PX`````````]0D`7M$`.<L`.<L`.<L`"
  "UOH`````````N^T`-\\H`-\\D`-LD`S/4`````````````````````````````````"
  "`````````````````````@\\`AN4`4ML`4ML`4ML`4=L`4=L`4=H`4-H`4-H`4-H`"
  "3]D`3]D`3]D`3MD`3MD`3M@`3=@`3=@`3=@`3-<`3-<`3-<`2]<`2]8`2]8`2M8`"
  "2M8`2M8`2=4`2=4`2=4`2-4`2-4`2-0`1]0`1]0`1M0`1M,`1M,`1=,`1=,`1=,`"
  "1-(`1-(`1-(`0](`0]$`0]$`0M$`0M$`0M$`0<``0<``0<``0,``0,\\`0,\\`/\\\\`"
  "/\\\\`/\\X`/LX`/LX`/LX`/<X`/<T`/<T`/,T`/,T`/,T`.\\P`C]X`_`X`````````"
  "W/P`.<L`.<L`.,L`;=,``0X`````]PD`/<H`-LD`-LD`A]H`````````````````"
  "````````````````````````````````````TOP`4]L`4ML`4ML`4ML`4=L`4=H`"
  "4-H`4-H`4-H`3]H`3]D`3]D`3MD`3MD`3M@`3=@`3=@`3=@`3-<`3-<`3-<`2]<`"
  "2]<`2]8`2M8`2M8`2M8`2=4`2=4`2=4`2-4`2-4`2-0`1]0`1]0`1]0`1M,`1M,`"
  "1M,`1=,`1=,`1=(`1-(`1-(`0](`0](`0]$`0M$`0M$`0M$`0<``0<``0<``0,``"
  "0,\\`0,\\`/\\\\`/\\\\`/\\\\`/LX`/LX`/LX`/<X`/<T`/<T`/,T`/,T`/,T`.\\P`.\\P`"
  ".\\P`J^@`````````````GN,`.<H`.,H`.,H`TO@`````````F=``-LD`-LD`3,P`"
  "````````````````````````````````````````````````````?N,`4ML`4ML`"
  "4ML`4=L`4=L`4=H`4-H`4-H`4-H`3]D`3]D`3]D`3MD`3M@`3M@`3=@`3=@`3=@`"
  "3-<`3-<`3-<`2]<`2]<`2M8`2M8`2M8`2=4`2=4`2=4`2-4`2-4`2-0`2-0`1]0`"
  "1]0`1M0`1M,`1M,`1=,`1=,`1=,`1-(`1-(`1-(`0]$`0]$`0]$`0M$`0M$`0L``"
  "0<``0<``0<``0,``0,\\`0,\\`/\\\\`/\\\\`/\\\\`/LX`/LX`/LX`/<X`/<T`/,T`/,T`"
  "/,T`.\\P`.\\P`.\\P`.LP`.LP`X/X`````````[`8`.,H`.,H`.,H`A-H`````````"
  "Y`$`3<P`-LD`N^T`````````````````````````````````````````````````"
  "YP0`4]P`4ML`4ML`4ML`4=L`4=H`4=H`4-H`4-H`4-H`3]D`3]D`3MD`3MD`3M@`"
  "3=@`3=@`3=@`3-@`3-<`3-<`2]<`2]<`2]8`2M8`2M8`2M8`2=4`2=4`2=4`2-4`"
  "2-4`2-0`1]0`1]0`1]0`1M,`1M,`1M,`1=,`1=,`1=(`1-(`1-(`1-(`0](`0]$`"
  "0M$`0M$`0M$`0<``0<``0<``0,``0,``0,\\`/\\\\`/\\\\`/\\\\`/LX`/LX`/LX`/<X`"
  "/<T`/<T`/,T`/,T`/,T`.\\P`.\\P`.\\P`.LP`.LL`@=H`````````````F-``.,H`"
  ".,H`-\\H`]0@`````````_0P`\\`@`````````````````````````````````````"
  "````````````````OO4`4ML`4ML`4ML`4=L`4=L`4=H`4-H`4-H`4-H`3]H`3]D`"
  "3]D`3MD`3MD`3M@`3=@`3=@`3=@`3-<`3-<`3-<`2]<`2]<`2]8`2M8`2M8`2M8`"
  "2=4`2=4`2=4`2-4`2-4`2-0`1]0`1]0`1M0`1M,`1M,`1=,`1=,`1=,`1-(`1-(`"
  "1-(`0](`0]$`0]$`0M$`0M$`0M$`0<``0<``0<``0,``0,\\`0,\\`/\\\\`/\\\\`/\\\\`"
  "/LX`/LX`/LX`/<X`/<T`/<T`/,T`/,T`/,T`.\\P`.\\P`.LP`.LP`.LL`.LL`YP$`"
  "````````VOL`.,H`-\\H`0,L`]`H`````````````````````````````````````"
  "````````````````````````````````D.@`4ML`4ML`4ML`4=L`4=H`4=H`4-H`"
  "4-H`4-H`3]D`3]D`3]D`3MD`3MD`3M@`3=@`3=@`3=@`3-<`3-<`3-<`2]<`2]<`"
  "2M8`2M8`2M8`2=8`2=4`2=4`2-4`2-4`2-0`1]0`1]0`1]0`1M0`1M,`1M,`1=,`"
  "1=,`1=(`1-(`1-(`1-(`0](`0]$`0M$`0M$`0M$`0L``0<``0<``0<``0,\\`0,\\`"
  "0,\\`/\\\\`/\\\\`/LX`/LX`/LX`/<X`/<X`/<T`/,T`/,T`/,T`.\\P`.\\P`.\\P`.LP`"
  ".LP`.LL`.<L`O.X`````````````Q?(`D]\\`V_P`````````````````````````"
  "````````````````````````````````````````````````6MT`4ML`4ML`4ML`"
  "4=H`4=H`4-H`4-H`4-H`3]D`3]D`3]D`3MD`3MD`3M@`3=@`3=@`3=@`3-@`3-<`"
  "3-<`2]<`2]<`2]8`2M8`2M8`2M8`2=4`2=4`2=4`2-4`2-4`1]0`1]0`1]0`1]0`"
  "1M0`1M,`1M,`1=,`1=,`1=(`1-(`1-(`0](`0]$`0]$`0M$`0M$`0M$`0<``0<``"
  "0<``0,``0,\\`0,\\`/\\\\`/\\\\`/\\\\`/LX`/LX`/LX`/<X`/<T`/<T`/,T`/,T`/,T`"
  ".\\P`.\\P`.LP`.LP`.LL`.<L`.<L`CMT`````````````````````````````````"
  "````````````````````````````````````````````````````````````_PX`"
  "4ML`4ML`4ML`4=L`4=H`4=H`4-H`4-H`4-H`3]D`3]D`3]D`3MD`3M@`3M@`3=@`"
  "3=@`3=@`3-<`3-<`2]<`2]<`2]8`2M8`2M8`2M8`2=8`2=4`2=4`2-4`2-4`2-0`"
  "1]0`1]0`1]0`1M0`1M,`1M,`1=,`1=,`1=(`1-(`1-(`1-(`0](`0]$`0]$`0M$`"
  "0M$`0<``0<``0<``0,``0,``0,\\`/\\\\`/\\\\`/\\\\`/LX`/LX`/LX`/<X`/<T`/<T`"
  "/,T`/,T`/,T`.\\P`.\\P`.\\P`.LP`.LL`.LL`.<L`.<L`<-4`````````````````"
  "````````````````````````````````````````````````````````````````"
  "`````0\\`[@<`W@$`4ML`4ML`4=L`4=L`4=H`4-H`4-H`4-H`3]D`3]D`3]D`3MD`"
  "3MD`3M@`3=@`3=@`3=@`3-<`3-<`3-<`2]<`2]<`2]8`2M8`2M8`2M8`2=4`2=4`"
  "2-4`2-4`2-0`1]0`1]0`1]0`1M0`1M,`1M,`1=,`1=,`1=,`1-(`1-(`1-(`0](`"
  "0]$`0]$`0M$`0M$`0L``0<``0<``0<``0,``0,\\`0,\\`/\\\\`/\\\\`/\\X`/LX`/LX`"
  "/LX`/<X`/<T`/<T`/,T`/,T`.\\P`.\\P`.\\P`.LP`.LP`.LL`.<L`.<L`.<L`3\\X`"
  "````````````````````````````````````````````````````````````````"
  "````````_@T`SOL`E>D`5=P`4]L`4ML`4ML`4ML`4=L`4=H`4=H`4-H`4-H`4-H`"
  "3]D`3]D`3MD`3M@`3M@`3=@`3=@`3=@`3-<`3-<`3-<`2]<`2]<`2]8`2M8`2M8`"
  "2M8`2=4`2=4`2=4`2-4`2-4`2-0`1]0`1]0`1]0`1M,`1M,`1=,`1=,`1=,`1-(`"
  "1-(`1-(`0](`0]$`0]$`0M$`0M$`0M$`0<``0<``0<``0,``0,\\`0,\\`/\\\\`/\\\\`"
  "/\\X`/LX`/LX`/LX`/<X`/<T`/<T`/,T`/,T`/,P`.\\P`.\\P`.\\P`.LP`.LL`.LL`"
  ".<L`.<L`.,H`;=,`````````````````````````````````````````````````"
  "````````````````````TOT`;-``4]P`4]P`4]P`4ML`4ML`4ML`4=L`4=H`4=H`"
  "4-H`4-H`4-H`3]D`3]D`3]D`3MD`3M@`3M@`3=@`3=@`3=@`3-<`3-<`2]<`2]<`"
  "2]8`2]8`2M8`2M8`2M8`2=4`2=4`2-4`2-4`2-4`1]0`1]0`1]0`1M,`1M,`1M,`"
  "1=,`1=,`1=(`1-(`1-(`1-(`0](`0]$`0]$`0M$`0M$`0M$`0<``0<``0<``0,``"
  "0,\\`/\\\\`/\\\\`/\\\\`/\\X`/LX`/LX`/<X`/<X`/<T`/,T`/,T`/,T`/,T`.\\P`.\\P`"
  ".LP`.LP`.LL`.<L`.<L`.<L`.,H`C=P`````````````````````````````````"
  "````````````````````````````_`X`I>X`5-P`5-P`4]P`4]P`4]P`4ML`4ML`"
  "4ML`4=L`4=H`4=H`4-H`4-H`4-H`3]D`3]D`3]D`3MD`3M@`3=@`3=@`3=@`3=@`"
  "3-<`3-<`2]<`2]<`2]8`2M8`2M8`2M8`2=8`2=4`2=4`2-4`2-4`2-0`1]0`1]0`"
  "1]0`1M0`1M,`1M,`1=,`1=,`1=(`1-(`1-(`1-(`0]$`0]$`0]$`0M$`0M$`0L``"
  "0<``0<``0<``0,\\`0,\\`/\\\\`/\\\\`/\\\\`/LX`/LX`/LX`/<X`/<T`/<T`/,T`/,T`"
  "/,T`.\\P`.\\P`.\\P`.LP`.LL`.LL`.<L`.<L`.<L`.,H`6\\\\`I^4`W?T``P``````"
  "````````````````````````````````````````_`X`F.H`5-T`5-P`5-P`4]P`"
  "4]P`4ML`4ML`4ML`4=L`4=L`4=H`4-H`4-H`4-H`3]D`3]D`3]D`3MD`3MD`3M@`"
  "3=@`3=@`3=@`3-<`3-<`3-<`2]<`2]8`2]8`2M8`2M8`2M8`2=4`2=4`2=4`2-4`"
  "2-4`2-0`1]0`1]0`1M0`1M0`1M,`1M,`1=,`1=,`1-(`1-(`1-(`0](`0]$`0]$`"
  "0M$`0M$`0M$`0<``0<``0<``0,``0,\\`0,\\`/\\\\`/\\\\`/\\\\`/LX`/LX`/LX`/<X`"
  "/<T`/<T`/,T`/,T`/,T`.\\P`.\\P`.LP`.LP`.LL`.<L`.<L`.<L`.,L`.,H`.,H`"
  "-\\H`-\\H`>]8`Y@$`````````````````````````````````````````KO$`5-T`"
  "5-P`5-P`4]P`4]P`4]L`4ML`4ML`4ML`4=L`4=L`4=H`4-H`4-H`4-H`3]D`3]D`"
  "3]D`3MD`3MD`3=@`3=@`3=@`3=@`3-<`3-<`3-<`2]<`2]8`2M8`2M8`2M8`2M8`"
  "2=4`2=4`2-4`2-4`2-4`1]0`1]0`1]0`1M0`1M,`1M,`1=,`1=,`1=(`1-(`1-(`"
  "1-(`0](`0]$`0]$`0M$`0M$`0M$`0<``0<``0<``0,``0,\\`/\\\\`/\\\\`/\\\\`/LX`"
  "/LX`/LX`/<X`/<X`/<T`/,T`/,T`/,T`.\\P`.\\P`.\\P`.LP`.LP`.LL`.<L`.<L`"
  ".<L`.,H`.,H`-\\H`-\\H`-\\H`-\\D`-LD`Q?$`````````````````````````````"
  "````W`$`5=T`5-T`5-P`5-P`4]P`4]P`4ML`4ML`4ML`4ML`4=L`4=H`4-H`4-H`"
  "4-H`3]D`3]D`3]D`3MD`3MD`3M@`3=@`3=@`3=@`3-<`3-<`3-<`2]<`2]<`2]8`"
  "2M8`2M8`2M8`2=4`2=4`2=4`2-4`2-4`2-0`1]0`1]0`1]0`1M,`1M,`1=,`1=,`"
  "1=,`1-(`1-(`1-(`0](`0]$`0]$`0M$`0M$`0M$`0<``0<``0<``0,``0,\\`0,\\`"
  "/\\\\`/\\\\`/\\\\`/LX`/LX`/LX`/<X`/<T`/,T`/,T`/,T`/,T`.\\P`.\\P`.\\P`.LP`"
  ".LL`.<L`.<L`.<L`.,L`.,H`.,H`-\\H`-\\H`-\\D`-LD`-LD`-LD`P>``````````"
  "````````````````````A>8`5-T`5-P`5-P`4]P`4]P`4]P`4ML`4ML`4ML`4=L`"
  "4=H`4=H`4-H`4-H`4-H`3]D`3]D`3]D`3MD`3M@`3=@`3=@`3=@`3-@`3-<`3-<`"
  "2]<`2]<`2]8`2M8`2M8`2M8`2=4`2=4`2=4`2-4`2-4`2-0`1]0`1]0`1]0`1M0`"
  "1M,`1M,`1=,`1=,`1=(`1-(`1-(`0](`0]$`0]$`0]$`0M$`0M$`0<``0<``0<``"
  "0,``0,``0,\\`/\\\\`/\\\\`/\\\\`/LX`/LX`/LX`/<X`/<T`/<T`/,T`/,T`/,T`.\\P`"
  ".\\P`.\\P`.LP`.LL`.LL`.<L`.<L`.<L`.,H`.,H`.,H`-\\H`-\\D`-\\D`-LD`-LD`"
  "-<D`-<@`W_T`````````````````````X`,`5=T`5-P`5-P`4]P`4]P`4]P`4ML`"
  "4ML`4ML`4=L`4=L`4=H`4-H`4-H`4-H`3]D`3]D`3]D`3MD`3M@`3M@`3=@`3=@`"
  "3=@`3-<`3-<`3-<`2]<`2]<`2M8`2M8`2M8`2=8`2=4`2=4`2=4`2-4`2-4`1]0`"
  "1]0`1]0`1M0`1M,`1M,`1=,`1=,`1=(`1-(`1-(`1-(`0](`0]$`0]$`0M$`0M$`"
  "0L``0<``0<``0<``0,``0,\\`/\\\\`/\\\\`/\\\\`/LX`/LX`/LX`/<X`/<T`/<T`/,T`"
  "/,T`/,T`.\\P`.\\P`.\\P`.LP`.LP`.LL`.<L`.<L`.<L`.,H`.,H`.,H`-\\H`-\\H`"
  "-\\D`-LD`-LD`-LD`-<@`-<@`;=(``0X`````````````````N/0`5-T`5-P`5-P`"
  "4]P`4]P`4]L`4ML`4ML`4ML`4=L`4=H`4-H`4-H`4-H`3]D`3]D`3]D`3MD`3MD`"
  "3M@`3=@`3=@`3=@`3-<`3-<`3-<`2]<`2]<`2]8`2M8`2M8`2M8`2=4`2=4`2=4`"
  "2-4`2-4`2-0`1]0`1]0`1]0`1M,`1M,`1M,`1=,`1=,`1=(`1-(`1-(`0](`0]$`"
  "0]$`0M$`0M$`0M$`0<``0<``0<``0,``0,\\`0,\\`/\\\\`/\\\\`/\\\\`/LX`/LX`/LX`"
  "/<X`/<T`/<T`/,T`/,T`/,T`.\\P`.\\P`.\\P`.LP`.LL`.<L`.<L`.<L`.<L`.,H`"
  ".,H`-\\H`-\\H`-\\D`-LD`-LD`-LD`-<@`-<@`-<@`-,@`T?8`````````````````"
  "C.<`5-T`5-P`4]P`4]P`4]P`4ML`4ML`4ML`4=L`4=L`4=H`4-H`4-H`4-H`3]D`"
  "3]D`3]D`3MD`3MD`3M@`3=@`3=@`3=@`3-<`3-<`3-<`2]<`2]<`2]8`2M8`2M8`"
  "2M8`2=4`2=4`2-4`2-4`2-0`1]0`1]0`1]0`1M0`1M,`1M,`1=,`1=,`1=(`1-(`"
  "1-(`1-(`0](`0]$`0]$`0M$`0M$`0L``0<``0<``0<``0,``0,\\`0,\\`/\\\\`/\\\\`"
  "/\\X`/LX`/LX`/LX`/<X`/<T`/<T`/,T`/,T`.\\P`.\\P`.\\P`.LP`.LP`.LL`.<L`"
  ".<L`.<L`.,H`.,H`.,H`-\\H`-\\H`-\\D`-LD`-LD`-LD`-<@`-<@`-<@`-,@`D-P`"
  "````````````````:=``5-P`5-P`4]P`4]P`4]P`4ML`4ML`4ML`4=L`4=H`4=H`"
  "4-H`4-H`4-H`3]D`3]D`3]D`3MD`3MD`3M@`3=@`3=@`3-@`3-<`3-<`2]<`2]<`"
  "2]8`2M8`2M8`2M8`2=8`2=4`2=4`2-4`2-4`2-0`1]0`1]0`1]0`1M0`1M,`1M,`"
  "1=,`1=,`1=(`1-(`1-(`1-(`0](`0]$`0]$`0M$`0M$`0L``0<``0<``0<``0,\\`"
  "0,\\`/\\\\`/\\\\`/\\\\`/LX`/LX`/LX`/<X`/<X`/<T`/,T`/,T`/,T`.\\P`.\\P`.\\P`"
  ".LP`.LL`.LL`.<L`.<L`.<L`.,H`.,H`.,H`-\\H`-\\H`-\\D`-LD`-LD`-LD`-<@`"
  "-<@`-,@`-,@`/<@``0X`````````````5]T`5-P`4]P`4]P`4]P`4]P`4ML`4ML`"
  "4=L`4=L`4=H`4-H`4-H`4-H`3]D`3]D`3]D`3MD`3MD`3M@`3=@`3=@`3=@`3-<`"
  "3-<`3-<`2]<`2]<`2]8`2M8`2M8`2=8`2=4`2=4`2=4`2-4`2-0`2-0`1]0`1]0`"
  "1]0`1M,`1M,`1=,`1=,`1=,`1-(`1-(`1-(`0](`0]$`0]$`0M$`0M$`0M$`0<``"
  "0<``0<``0,``0,\\`0,\\`/\\\\`/\\\\`/\\\\`/LX`/LX`/LX`/<X`/<T`/<T`/,T`/,T`"
  ".\\P`.\\P`.\\P`.\\P`.LP`.LL`.LL`.<L`.<L`.,H`.,H`.,H`-\\H`-\\H`-\\D`-LD`"
  "-LD`-LD`-<@`-<@`-<@`-,@`-,@`-,<`[`4`````````````9]\\`5-P`4]P`4]P`"
  "4]P`4ML`4ML`4ML`4=L`4=H`4=H`4-H`4-H`4-H`3]D`3]D`3MD`3MD`3MD`3M@`"
  "3=@`3=@`3=@`3-<`3-<`3-<`2]<`2]8`2M8`2M8`2M8`2=8`2=4`2=4`2-4`2-4`"
  "2-0`1]0`1]0`1]0`1M0`1M,`1M,`1=,`1=,`1=,`1-(`1-(`1-(`0](`0]$`0M$`"
  "0M$`0M$`0L``0<``0<``0,``0,``0,\\`/\\\\`/\\\\`/\\\\`/\\X`/LX`/LX`/<X`/<T`"
  "/<T`/,T`/,T`/,T`.\\P`.\\P`.\\P`.LP`.LP`.LL`.<L`.<L`.<L`.,L`.,H`.,H`"
  "-\\H`-\\D`-\\D`-LD`-LD`-LD`-<@`-<@`-<@`-,@`-,<`,\\<`Y`$`````````````"
  "B.8`5-P`4]P`4]P`4ML`4ML`4ML`4=L`4=L`4=H`4-H`4-H`4-H`3]H`3]D`3]D`"
  "3MD`3MD`3M@`3=@`3=@`3=@`3-<`3-<`3-<`2]<`2]<`2]8`2M8`2M8`2M8`2=4`"
  "2=4`2=4`2-4`2-4`2-0`1]0`1]0`1M0`1M,`1M,`1=,`1=,`1=,`1-(`1-(`1-(`"
  "0](`0]$`0]$`0M$`0M$`0M$`0<``0<``0<``0,``0,\\`0,\\`/\\\\`/\\\\`/\\\\`/LX`"
  "/LX`/LX`/<X`/<T`/,T`/,T`/,T`.\\P`.\\P`.\\P`.LP`.LP`.LL`.<L`.<L`.<L`"
  ".<L`.,H`.,H`-\\H`-\\H`-\\D`-LD`-LD`-LD`-<@`-<@`-<@`-,@`-,@`-,<`,\\<`"
  "Z`,`````````````L_(`4]P`4]P`4]P`4ML`4ML`4ML`4=L`4=H`4-H`4-H`4-H`"
  "3]D`3]D`3]D`3MD`3MD`3M@`3=@`3=@`3=@`3-@`3-<`3-<`2]<`2]<`2]8`2M8`"
  "2M8`2M8`2=4`2=4`2=4`2-4`2-4`2-0`1]0`1]0`1]0`1M,`1M,`1M,`1=,`1=,`"
  "1=(`1-(`1-(`1-(`0]$`0]$`0M$`0M$`0M$`0<``0<``0<``0,``0,\\`0,\\`/\\\\`"
  "/\\\\`/\\\\`/LX`/LX`/LX`/<X`/<T`/<T`/,T`/,T`/,T`.\\P`.\\P`.LP`.LP`.LL`"
  ".LL`.<L`.<L`.<L`.,H`.,H`.,H`-\\H`-\\D`-LD`-LD`-LD`-<@`-<@`-<@`-,@`"
  "-,@`-,<`,\\<`,\\<`^`P`````````````W`$`4]P`4]P`4ML`4ML`4ML`4=L`4=H`"
  "4=H`4-H`4-H`4-H`3]D`3]D`3]D`3MD`3MD`3M@`3=@`3=@`3-<`3-<`3-<`3-<`"
  "2]<`2]8`2M8`2M8`2M8`2=8`2=4`2=4`2-4`2-4`2-0`1]0`1]0`1]0`1M0`1M,`"
  "1M,`1=,`1=,`1=(`1-(`1-(`1-(`0](`0]$`0]$`0M$`0M$`0L``0<``0<``0<``"
  "0,\\`0,\\`/\\\\`/\\\\`/\\\\`/LX`/LX`/LX`/<X`/<T`/<T`/,T`/,T`/,T`.\\P`.\\P`"
  ".\\P`.LP`.LL`.LL`.<L`.<L`.<L`.,H`.,H`.,H`-\\H`-\\D`-\\D`-LD`-LD`-LD`"
  "-<@`-<@`-,@`-,@`-,<`,\\<`,\\<`>-0``````````````````@\\`>>,`4]P`4ML`"
  "4ML`4ML`4=L`4=H`4=H`4-H`4-H`3]H`3]D`3]D`3MD`3MD`3M@`3=@`3=@`3=@`"
  "3-<`3-<`3-<`2]<`2]<`2]8`2M8`2M8`2M8`2=4`2=4`2=4`2-4`2-4`2-0`1]0`"
  "1]0`1]0`1M0`1M,`1=,`1=,`1=,`1-(`1-(`1-(`1-(`0]$`0]$`0]$`0M$`0M$`"
  "0<``0<``0<``0,``0,``0,\\`/\\\\`/\\\\`/\\\\`/LX`/LX`/LX`/<X`/<T`/<T`/,T`"
  "/,T`/,T`.\\P`.\\P`.\\P`.LP`.LL`.LL`.<L`.<L`.<L`.,H`.,H`-\\H`-\\H`-\\D`"
  "-LD`-LD`-LD`-<D`-<@`-<@`-,@`-,@`-,@`,\\<`,\\<`P.\\`````````````````"
  "````U_X`4ML`4ML`4ML`4=L`4=L`4=H`4-H`4-H`4-H`3]D`3]D`3]D`3MD`3M@`"
  "3M@`3=@`3=@`3=@`3-<`3-<`3-<`2]<`2]<`2]8`2M8`2M8`2M8`2=4`2=4`2=4`"
  "2-4`2-4`2-0`1]0`1]0`1M0`1M,`1M,`1=,`1=,`1=,`1-(`1-(`1-(`0](`0]$`"
  "0]$`0M$`0M$`0L``0<``0<``0<``0,``0,\\`0,\\`/\\\\`/\\\\`/\\X`/LX`/LX`/LX`"
  "/<X`/<T`/,T`/,T`/,T`/,P`.\\P`.\\P`.LP`.LP`.LL`.<L`.<L`.<L`.,H`.,H`"
  ".,H`-\\H`-\\H`-\\D`-LD`-LD`-LD`-<@`-<@`-<@`-,@`-,@`-,<`,\\<`2\\H`^0H`"
  "````````````````````````HNP`4ML`4ML`4=L`4=H`4=H`4-H`4-H`4-H`3]D`"
  "3]D`3]D`3MD`3M@`3=@`3=@`3=@`3-@`3-<`3-<`3-<`2]<`2]<`2M8`2M8`2M8`"
  "2=8`2=4`2=4`2-4`2-4`2-0`1]0`1]0`1]0`1M0`1M,`1M,`1=,`1=,`1=(`1-(`"
  "1-(`1-(`0](`0]$`0]$`0M$`0M$`0L``0<``0<``0,``0,``0,\\`/\\\\`/\\\\`/\\\\`"
  "/LX`/LX`/LX`/<X`/<X`/<T`/,T`/,T`/,T`.\\P`.\\P`.\\P`.LP`.LP`.LL`.<L`"
  ".<L`.<L`.,H`.,H`.,H`-\\H`-\\D`-\\D`-LD`-LD`-LD`-<@`-<@`-,@`-,@`-,@`"
  ",\\<`,\\<`Q?$`````````````````````````````_0T`A^4`4ML`4=L`4=H`4-H`"
  "4-H`4-H`3]D`3]D`3]D`3MD`3MD`3M@`3=@`3=@`3=@`3-<`3-<`3-<`2]<`2]8`"
  "2]8`2M8`2M8`2M8`2=4`2=4`2=4`2-4`2-4`2-0`1]0`1]0`1M0`1M,`1M,`1=,`"
  "1=,`1=,`1-(`1-(`1-(`0](`0]$`0]$`0M$`0M$`0M$`0<``0<``0<``0,``0,\\`"
  "0,\\`/\\\\`/\\\\`/LX`/LX`/LX`/LX`/<X`/<T`/<T`/,T`/,T`/,T`.\\P`.\\P`.LP`"
  ".LP`.LL`.<L`.<L`.<L`.,L`.,H`.,H`-\\H`-\\H`-\\D`-LD`-LD`-LD`-<D`-<@`"
  "-<@`-,@`-,@`-,<`,\\<`E]X``P``````````````````````````````````^`P`"
  "E.@`4=H`4=H`4-H`4-H`4-H`3]D`3]D`3]D`3MD`3M@`3=@`3=@`3=@`3-@`3-<`"
  "3-<`2]<`2]<`2]8`2M8`2M8`2M8`2=8`2=4`2=4`2-4`2-4`2-0`1]0`1]0`1]0`"
  "1M0`1M,`1M,`1=,`1=,`1=(`1-(`1-(`0](`0](`0]$`0]$`0M$`0M$`0L``0<``"
  "0<``0,``0,\\`0,\\`/\\\\`/\\\\`/\\\\`/LX`/LX`/LX`/<X`/<X`/<T`/,T`/,T`/,T`"
  ".\\P`.\\P`.\\P`.LP`.LL`.LL`.<L`.<L`.<L`.,H`.,H`.,H`-\\H`-\\H`-LD`-LD`"
  "-LD`-<D`-<@`-<@`-,@`-,@`-,@`,\\<`E=X`_PT`````````````````````````"
  "`````````````````@\\`Q/<`6ML`4-H`4-H`3]D`3]D`3]D`3MD`3MD`3M@`3=@`"
  "3=@`3=@`3-<`3-<`3-<`2]<`2]8`2]8`2M8`2M8`2M8`2=4`2=4`2-4`2-4`2-4`"
  "1]0`1]0`1]0`1M0`1M,`1M,`1=,`1=,`1=(`1-(`1-(`1-(`0](`0]$`0]$`0M$`"
  "0M$`0M$`0<``0<``0<``0,``0,\\`0,\\`/\\\\`/\\\\`/\\X`/LX`/LX`/LX`/<X`/<T`"
  "/<T`/,T`/,T`.\\P`.\\P`.\\P`.LP`.LP`.LL`.<L`.<L`.<L`.,H`.,H`.,H`-\\H`"
  "-\\H`-\\D`-LD`-LD`-LD`-<@`-<@`-<@`-,@`-,@`0,@`P.X``@\\`````````````"
  "````````````````````````````````````````]`L`P/4`>.$`3]D`3]D`3MD`"
  "3M@`3M@`3=@`3=@`3=@`3-<`3-<`3-<`2]<`2]<`2]8`2M8`2M8`2M8`2=4`2=4`"
  "2=4`2-4`2-4`2-0`1]0`1]0`1M0`1M,`1M,`1=,`1=,`1=,`1-(`1-(`1-(`0](`"
  "0](`0]$`0M$`0M$`0L``0<``0<``0<``0,``0,\\`0,\\`/\\\\`/\\\\`/\\\\`/LX`/LX`"
  "/LX`/<X`/<T`/<T`/,T`/,T`/,T`.\\P`.\\P`.\\P`.LP`.LL`.LL`.<L`.<L`.<L`"
  ".,H`.,H`-\\H`-\\H`-\\D`-LD`-LD`-LD`-<D`-<@`-<@`-,@`7\\\\`M.H`\\`@`````"
  "````````````````````````````````````````````````````````````````"
  "````]@H`Y@,`U?T`V?X`ZP4`Z`4`Z`4`Z`4`Z`4`Z`4`Z`4`Z`4`Z@4`Z00`Z00`"
  "Z00`Y`0`Y`,`Y`,`YP,`YP,`YP,`Y@,`Y@(`Y@(`Y0(`Y0(`Y0$`X`$`X`$`X`$`"
  "XP$`XO``X?``X?``X?``X/\\`X/\\`X/\\`W_\\`W_\\`WO\\`WOX`W?X`W?X`W?X`W/T`"
  "W/T`W/T`V_T`V_P`V_P`VOP`VOP`VOP`V?L`V/L`V/L`V/L`U_H`U_H`U_H`UOH`"
  "UOD`U?D`U?D`U/D`U/D`U/@`T_@`T_@`T_@`TO<`T?<`T?<`T?<`T?<`WOT`[`8`"
  "````````````````````````````````````````````````````````````````"
  "````````````````````````````````````````````````````````````````"
  "````````````````````````````````````````````````````````````````"
  "````````````````````````````````````````````````````````````````"
  "````````````````````````````````````````````````````````````````"
  "````````````````````````````````````````````````````````````````"
  "````````````````````````````````````````````````````````````````"
  "````````````````````````````````````````````````````````````````"
  "````````````````````````````````````````````````````````````````"
  "````````````````````````````````````````````````````````````````"
  "````````````````````````````````````````````````````````````````"
  "````````````````````````````````````````````````````````````````"
  "````````````````````````````````````````````````````````````````"
  "````````````````````````````````````````````````````````````````"
  "````````````````````````````````````````````````````````````````"
  "````````````````````````````````````````````````````````````````"
  "````````````````````````````````````````````````````````````````"
  "````````````````````````````````````````````````````````````````"
  "````````````````````````````````````````````````````````````````"
  "````````````````````````````````````````````````````````````````"
  "````````````````````````````````````````````````````````````````"
  "````````````````````````````````````````````````````````````````"
  "````````````````````````````````````````````````````````````````"
  "````````````````````````````````````````````````````````````````"
  "````````````````````````````````````````````````````````````````"
  "````````````````````````````````````````````````````````````````"
  "````````````````````````````````````````````````````````````````"
  "````````````````````````````````````````````````````````````````"
  "````````````````````````````````````````````````````````````````"
  "````````````````````````````````````````````````````````````````"
  "````````````````````````````````````````````````````````````````"
  "````````````````````````````````````````````````````````````````"
  "````````````````````````````````````````````````````````````````"
  "````````````````````````````````````````````````````````````````"
  "````````````````````````````````````````````````````````````````"
  "````````````````````````````````````````````````````````````````"
  "````````````````````````````````````````````````````````````````"
  "````````````````````````````````````````````````````````````````"
  "````````````````````````````````````````````````````````````````"
  "````````````````````````````````````````````````````````````````"
  "````````````````````````````````````````````````````````````````"
  "````````````````````````````````````````````````````````````````"
  "````````````````````````````````````````````````````````````````"
  "````````````````````````````````````````````````````````````````"
  "````````````````````````````````````````````]`0T[/DI[/DI[/DI[/DI"
  "[/DI[OLK````````\\/TM[/DI^P<W````````````]`0T[/DI\\_`P````````_PL["
  "[/DI[/DI[/DI[/DI[/DI_PL[`````````````````````P\\_[/DI[/DI[/DI[/DI"
  "[/DI[/DI^@8V````_0DY[/DI[OLK`````````````P\\_[/DI[/DI_`P\\````````"
  "\\O\\O[/DI^04U````````^P<W[/DI\\_`P````````````````[OLK[/DI_`P\\````"
  "````````````````\\_`PUN,3TM\\/X>X>_`P\\````````````````````````_PL["
  "W.D9TM\\/Y/$A`P\\_````````````````````````````````````````````A9'\""
  "!!!!!!!!!!!!!!!!!!!!!!!![/DI^`@X!!!!!!!!IK+C````````````@8V^!!!!"
  "1E*#````````PL[_!!!!!!!!!!!!!!!!!!!!P,S]````````````````````X.T="
  "!!!!!!!!!!!!!!!!!!!!!!!!FZ?8````L+SM!!!!!!!!\\?XN````````X^`@!!!!"
  "!!!!R-4%````````+CIK!!!!AY/$````````HZ_@!!!!+CIK\\?XN````````[OLK"
  "!!!!!!!!SML+````````````\\O\\OD9W.!!!!!!!!!!!!!!!!3UN,R]@(````````"
  "````````X.T=45V.!!!!!!!!!!!!>86V]0$Q````````````````````````````"
  "````````````A)#!!!!!!!!!!!!!!!!!!!!!!!!![/DI^@8V!!!!!!!!HJ[?````"
  "````````>X>X!!!!-D)S````````OLK[!!!!!!!!!!!!!!!!!!!!P,S]````````"
  "````````````X.T=!!!!!!!!!!!!!!!!!!!!!!!!FZ?8````K+CI!!!!!!!![_PL"
  "````````X>X>!!!!!!!!Q=(\"````````(\"Q=!!!!@8V^````````H*S=!!!!!!!!"
  "C9G*````````[OLK!!!!!!!!R]@(````````\\/TM3UN,!!!!!!!!!!!!!!!!!!!!"
  "!!!!!!!!KKKK````````^04U/$AY!!!!!!!!04U^!!!!!!!!DY_0````````````"
  "````````````````````````````]P,SZO<GDY_0!!!!!!!!X>X>[/DI````^@8V"
  "!!!!!!!!HJ[?````````````>X>X!!!!-D)S````````OLK[!!!!!!!!V.45ZO<G"
  "ZO<G_@HZ`````````````````````P\\_ZO<GUN,3!!!!!!!!GZO<ZO<G^04U````"
  "K+CI!!!!!!!![_PL````````X>X>!!!!!!!!Q=(\"````````(\"Q=!!!!@8V^````"
  "````H*S=!!!!!!!!!!!!U>(2````\\/TM!!!!!!!!R]@(````````?8FZ!!!!!!!!"
  "J[?H]`0T`@X^V.451%\"!!!!!!!!!VN<7````UN,3!!!!!!!!Q-$!`P\\_?HJ[/$AY"
  "3UN,````````````````````````````````````````````````HZ_@!!!!!!!!"
  "^@8V````````^@8V!!!!!!!!EZ/4\\O\\O\\O\\O\\O\\O<GZO!!!!-D)S````````OLK["
  "!!!!!!!!X^`@]`0T^04U````````````````````````````````[?HJ!!!!!!!!"
  "L+SM````````````K+CI!!!!!!!!W^P<\\O\\O\\O\\OTM\\/!!!!!!!!Q=(\"````````"
  "(\"Q=!!!!@8V^````````H*S=!!!!!!!!!!!!56&2_0DY\\O\\O!!!!!!!!R]@(````"
  "Z/4E!!!!!!!!DI[/````````````````Z_@HS-D)S-D)Y_0D````X.T=!!!!!!!!"
  "BI;']@(R````````````````````````````````````````````````````````"
  "````HZ_@!!!!!!!!^@8V````````^@8V!!!!!!!!!!!!!!!!!!!!!!!!!!!!!!!!"
  "-D)S````````OLK[!!!!!!!!!!!!!!!!!!!!UN,3````````````````````````"
  "````[?HJ!!!!!!!!L+SM````````````K+CI!!!!!!!!!!!!!!!!!!!!!!!!!!!!"
  "!!!!Q=(\"````````(\"Q=!!!!@8V^````````H*S=!!!!9'\"A@HZ_!!!!K[OL]0$Q"
  "!!!!!!!!R]@(````S-D)!!!!!!!!UN,3````\\O\\OML+SML+SML+SML+SML+SP<W^"
  "`````P\\_BI;'!!!!!!!!)C)CI;'B\\O\\O````````````````````````````````"
  "````````````````````HZ_@!!!!!!!!^@8V````````^@8V!!!!!!!!!!!!!!!!"
  "!!!!!!!!!!!!!!!!-D)S````````OLK[!!!!!!!!!!!!!!!!!!!!TM\\/````````"
  "````````````````````[?HJ!!!!!!!!L+SM````````````K+CI!!!!!!!!!!!!"
  "!!!!!!!!!!!!!!!!!!!!Q=(\"````````(\"Q=!!!!@8V^````````H*S=!!!!86V>"
  "[?HJ)C)C$1U.VN<7!!!!!!!!R]@(````R]@(!!!!!!!!W.D9````TM\\/!!!!!!!!"
  "!!!!!!!!!!!!!!!!````````_`P\\P<W^45V.!!!!!!!!-D)SV^@8````````````"
  "````````````````````````````````````HZ_@!!!!!!!!^@8V````````^@8V"
  "!!!!!!!!CIK+YO,CYO,CYO,C;7FJ!!!!-D)S````````OLK[!!!!!!!!R=8&V^@8"
  "V^@8_@HZ````````````````````````````[?HJ!!!!!!!!L+SM````````````"
  "K+CI!!!!!!!!U.$1YO,CYO,CR-4%!!!!!!!!Q=(\"````````(\"Q=!!!!@8V^````"
  "````H*S=!!!!6F:7````N,3U!!!!9'\"A!!!!!!!!R]@(````W.D9!!!!!!!!N,3U"
  "````[?HJIK+CIK+CE:'2!!!!!!!!<'RM`````````````````0T]SML+,CYO!!!!"
  "35F*`P\\_````````````````````````````````````````````HZ_@!!!!!!!!"
  "^@8V````````^@8V!!!!!!!!HJ[?````````````>X>X!!!!-D)S````````OLK["
  "!!!!!!!![_PL````````````````````````````````````````[?HJ!!!!!!!!"
  "L+SM````````````K+CI!!!!!!!![_PL````````X>X>!!!!!!!!Q=(\"````````"
  "(\"Q=!!!!@8V^````````H*S=!!!!4U^0````_PL[9W.D!!!!!!!!!!!!R]@(````"
  "_`P\\3UN,!!!!/$AYZ?8F`````````P\\_HZ_@!!!!!!!!P,S]````N\\?X*C9G*C9G"
  "Y/$A````GZO<!!!!!!!!]`0T````````````````````````````````````````"
  "````HZ_@!!!!!!!!^@8V````````^@8V!!!!!!!!HJ[?````````````>X>X!!!!"
  "-D)S````````OLK[!!!!!!!!;7FJ=H*S=H*SV.45````````````````````````"
  "````[?HJ!!!!!!!!L+SM````````````K+CI!!!!!!!![_PL````````X>X>!!!!"
  "!!!!Q=(\"````````(\"Q=!!!!@8V^````````H*S=!!!!2U>(````````X.T=!!!!"
  "!!!!!!!!R]@(````````U>(2!!!!!!!!)C)CF*35I[/D;7FJ!!!!!!!!:76F_@HZ"
  "````U.$1!!!!!!!!<GZOM<'R,CYO!!!!04U^`P\\_````````````````````````"
  "````````````````````HZ_@!!!!!!!!^@8V````````^@8V!!!!!!!!HJ[?````"
  "````````>X>X!!!!-D)S````````OLK[!!!!!!!!!!!!!!!!!!!!N\\?X````````"
  "````````````````````[?HJ!!!!!!!!L+SM````````````K+CI!!!!!!!![_PL"
  "````````X>X>!!!!!!!!Q=(\"````````(\"Q=!!!!@8V^````````H*S=!!!!1%\"!"
  "````````````HJ[?!!!!!!!!R]@(````````````RM<'*C9G!!!!!!!!!!!!!!!!"
  "!!!!<'RM\\O\\O`````````0T]?8FZ!!!!!!!!!!!!!!!!!!!!QM,#````````````"
  "````````````````````````````````````VN<7J[?HL[_P`P\\_`````````@X^"
  "LK[OJ[?HV^@8````````````SML+J[?HO\\O\\````````Z?8FJ[?HJ[?HJ[?HJ[?H"
  "J[?HZ/4E````````````````````````````_@HZL+SMJ[?HX.T=````````````"
  "X.T=J[?HL+SM_@HZ````````]`0TK+CIJ[?HZ_@H````````NL;WJ[?HT=X.````"
  "````V>86J[?HP,S]````````````^@8VKKKKJ[?H[?HJ````````````````\\O\\O"
  "N,3UB97&>X>XFZ?8T-T-`0T]````````````````_@HZP\\_`CYO,?8FZGJK;W.D9"
  "````````````````````````````````````````````````````````````````"
  "````````````````````````````````````````````````````````````````"
  "````````````````````````````````````````````````````````````````"
  "````````````````````````````````````````````````````````````````"
  "````````````````````````````````````````````````````````````````"
  "````````````````````````````````````````````````````````````````"
  "````````````````````````````````````````````````````````````````"
  "````````````````````````````````````````````````````````````````"
  "````````````````````````````````````````````````````````````````"
  "````````````````````````````````````````````````````````````````"
  "````````````````````````````````````````````````````````````````"
  "````````````````````````````````````````````````````````````````"
  "````````````````````````````````````````````````````````````````"
  "````````````````````````````````````````````````````````````````"
  "````````````````````````````````````````````````````````````````"
  "````````````````````````````````````````````````````````````````"
  "````````````````````````````````````````````````````````````````"
  "````````````````````````````````````````````````````````````````"
  "````````````````````````````````````````````````````````````````"
  "`````````````````````````````````````P\\_`````````````````````P\\_"
  "`````````````````````````````P\\_`P\\_`P\\_`P\\_````````````````````"
  "`````P\\_`P\\_`P\\_`P\\_`P\\_`P\\_`````````````````````````P\\_````````"
  "`````````P\\_`````````````````P\\_````````````````````````````````"
  "`P\\_\\/TMZ_@H^P<W`````````````````````````````````````P\\_`P\\_`P\\_"
  "`````````````````````````````````````````P\\_````````````````````"
  "````````````````````````````````````````````````86V>!!!!D)S-````"
  "````````S]P,!!!!(\"Q=]0$Q````````````````04U^!!!!!!!!!!!!!!!!256&"
  "````````````````R]@(!!!!!!!!!!!!!!!!!!!!!!!!R-4%````````````[/DI"
  "!!!!!!!!S-D)````````HJ[?!!!!I[/D````````Q]0$!!!!!!!!\\?XN````````"
  "````````_PL[NL;W256&!!!!!!!!!!!!B97&Y_0D````````````````````````"
  "S=H*!!!!!!!!!!!!!!!!6666IK+C]`0T````````````````````:G:G!!!!B97&"
  "````````TM\\/!!!!!!!!Z/4E````````````````````````````````````````"
  ".45V!!!!!!!!U>(2````````Q]0$!!!!!!!!Z_@H`````````````P\\_!!!!!!!!"
  "!!!!!!!!!!!!!!!!````````````````P<W^!!!!!!!!!!!!!!!!!!!!!!!!OLK["
  "````````````_0DY$1U.!!!!GZO<````````5V.4!!!!9'\"A````````F*35!!!!"
  ",CYO`0T]````````````_@HZ@HZ_!!!!!!!!!!!!!!!!!!!!!!!!$1U.T-T-````"
  "````````````````P\\_`!!!!!!!!!!!!!!!!!!!!!!!!;7FJ_`P\\````````````"
  "````256&!!!!?(BY````^@8V2U>(!!!!@(R]`@X^````````````````````````"
  "````````````````.45V!!!!!!!!5V.4_0DY````RM<'!!!!!!!!Z_@H````````"
  "`````P\\_!!!!!!!!A)#!S=H*S=H*V>86````````````````]0$QS=H*I;'B!!!!"
  "!!!!I;'BS=H*\\O\\O````````````````@HZ_!!!!9'\"A````\\_`P!!!!!!!!!!!!"
  "]`0T````5V.4!!!!D)S-````````````````J[?H!!!!!!!!@(R]W.D9Z/4EO,CY"
  ")C)C!!!!*C9G[OLK````````````````P\\_`!!!!!!!!O\\O\\RM<'>H:W!!!!!!!!"
  "T]`0````````````````256&!!!!?(BY````HZ_@!!!!+CIK[_PL````````````"
  "````````````````````````````````.45V!!!!!!!!!!!!K[OL````S=H*!!!!"
  "!!!!Z_@H`````````````P\\_!!!!!!!!J+3E````````````````````````````"
  "````````T=X.!!!!!!!!T=X.````````````````````````NL;W!!!!!!!!^P<W"
  "U>(2!!!!)C)C!!!!VN<7]@(R!!!!!!!!P\\_`````````````^@8V(\"Q=!!!!<'RM"
  "_`P\\````````````S]P,!!!!!!!!I[/D````````````````P\\_`!!!!!!!!\\O\\O"
  "````\\O\\O!!!!!!!!KKKK````````````````256&!!!!?(BYX.T=!!!!!!!!PL[_"
  "````````````````````````````````````````````````.45V!!!!>X>X(\"Q="
  "$1U.ZO<GT-T-!!!!!!!!Z_@H`````````````P\\_!!!!!!!!.45V7&B97&B9EZ/4"
  "````````````````````````T=X.!!!!!!!!T=X.````````````````````````"
  "X.T=!!!!!!!!W^P<KKKK!!!!I;'B!!!!N,3UVN<7!!!!!!!!ZO<G````````````"
  "V.45!!!!!!!!R=8&`````````````````P\\_4U^0!!!!86V>````````````````"
  "P\\_`!!!!!!!!\\O\\O````ZO<G!!!!!!!!P<W^````````````````256&!!!!<'RM"
  ":76F!!!!?8FZ`@X^````````````````````````````````````````````````"
  ".45V!!!!I[/DML+S!!!!>X>XT=X.!!!!!!!!Z_@H`````````````P\\_!!!!!!!!"
  "!!!!!!!!!!!!;'BI````````````````````````T=X.!!!!!!!!T=X.````````"
  "````````````````_`P\\(\"Q=!!!!P<W^>86V!!!![OLK!!!!B97&N<7V!!!!35F*"
  "````````````````R]@(!!!!!!!!V>86````````````````````>86V!!!!1%\"!"
  "````````````````P\\_`!!!!!!!!HJ[?J[?H4U^0!!!!+CIK\\O\\O````````````"
  "````256&!!!!!!!!!!!!!!!!S-D)````````````````````````````````````"
  "````````````````.45V!!!!I;'B_PL[9'\"A!!!!@8V^!!!!!!!!Z_@H````````"
  "`````P\\_!!!!!!!!>X>XO\\O\\O\\O\\U.$1````````````````````````T=X.!!!!"
  "!!!!T=X.````````````````````````````BY?(!!!!C)C)!!!!=(\"Q````9'\"A"
  "+CIKBI;'!!!!G:G:````````````````U>(2!!!!!!!!O\\O\\````````````````"
  "_`P\\04U^!!!!=H*S````````````````P\\_`!!!!!!!!!!!!!!!!!!!!56&2V^@8"
  "````````````````````256&!!!!<7VN;GJK!!!!35F*]`0T````````````````"
  "````````````````````````````````.45V!!!!HZ_@````WNL;!!!!!!!!!!!!"
  "!!!!Z_@H`````````````P\\_!!!!!!!!I[/D````````````````````````````"
  "````````T=X.!!!!!!!!T=X.````````````````````````````O\\O\\!!!!!!!!"
  "!!!!K+CI````HZ_@!!!!!!!!!!!!S-D)````````````````]`0T(\"Q=!!!!35F*"
  "\\_`P````````````N,3U!!!!!!!!NL;W````````````````P\\_`!!!!!!!!?8FZ"
  "!!!!&B97YO,C````````````````````````256&!!!!?(BYX^`@!!!!!!!!DI[/"
  "````````````````````````````````````````````````.45V!!!!HZ_@````"
  "````GZO<!!!!!!!!!!!!Z_@H`````````````P\\_!!!!!!!!;'BIJ;7FJ;7FML+S"
  "````````````````````````T=X.!!!!!!!!T=X.````````````````````````"
  "````Y/$A!!!!!!!!!!!!U.$1````S=H*!!!!!!!!!!!!\\O\\O````````````````"
  "````ML+S!!!!!!!!35F*NL;WR]@(DY_0!!!!!!!!4U^0^P<W````````````````"
  "P\\_`!!!!!!!!Z?8F8&R=!!!!7&B9]`0T````````````````````256&!!!!?(BY"
  "````J+3E!!!!!!!!R=8&````````````````````````````````````````````"
  ".45V!!!!H:W>````````]`0T1E*#!!!!!!!!Z_@H`````````````P\\_!!!!!!!!"
  "!!!!!!!!!!!!!!!!````````````````````````T=X.!!!!!!!!T=X.````````"
  "`````````````````````@X^-D)S!!!!!!!!\\O\\O````[OLK!!!!!!!!8V^@````"
  "`````````````````````@X^I[/D!!!!!!!!!!!!!!!!!!!!!!!!35F*YO,C````"
  "````````````````P\\_`!!!!!!!!\\O\\OX^`@!!!!!!!!AY/$`0T]````````````"
  "````256&!!!!?(BY````^`@X4U^0!!!!,CYO[_PL````````````````````````"
  "````````````````G:G:?HJ[QM,#````````````U>(2?HJ[AY/$^@8V````````"
  "````````D9W.?HJ[?HJ[?HJ[?HJ[E:'2````````````````````````Z/4E@8V^"
  "@(R]YO,C````````````````````````````````ML+S?HJ[F*35````````````"
  "DY_0?HJ[P\\_`````````````````````````````````X.T=F*3545V.(\"Q=9W.D"
  "L[_P^04U````````````````````````W>H:?HJ[AY/$^`@X````Q=(\"?HJ[?HJ["
  "V.45````````````````HJ[??HJ[L+SM````````V^@8@(R]?HJ[VN<7````````"
  "````````````````";
